valenlysm29/FdD_EQUIPO02/Proyecto/Módulo Mecánico/Certificados/Rosita Espinola/Certificados de Rosita Espinola-1.pdf

ROSITA ABANTO

April 30, 2026

Detailed Drawings

ROSITA ABANTO

Introduction to Sketching

April 30, 2026

ROSITA ABANTO

Introduction to Part Studios

April 30, 2026

ROSITA ABANTO

April 30, 2026

Introduction to Onshape Assemblies

Onshape Fundamentals

April 30, 2026

ROSITA ABANTO

ROSITA ABANTO

CAD Basics

April 30, 2026
