valenlysm29/FdD_EQUIPO02/Proyecto/Módulo Mecánico/Certificados/Ayme Canchari/Certificados de Ayme Canchari-1.pdf

Onshape Fundamentals

April 30, 2026

Ayme Canchari

Ayme Canchari

Advanced Onshape Assemblies

May 21, 2026

Ayme Canchari

April 30, 2026

Introduction to Drawings

Ayme Canchari

April 30, 2026

Detailed Drawings

Ayme Canchari

Introduction to Sketching

April 30, 2026

Ayme Canchari

April 30, 2026

Introduction to Onshape Assemblies
