valenlysm29/FdD_EQUIPO02/FundDiseño/Talleres/Taller 7/Taller 7_certificados/Perez Salvatierra, Maria Fernanda/Maria Fernanda Perez Salvatierra (1).pdf

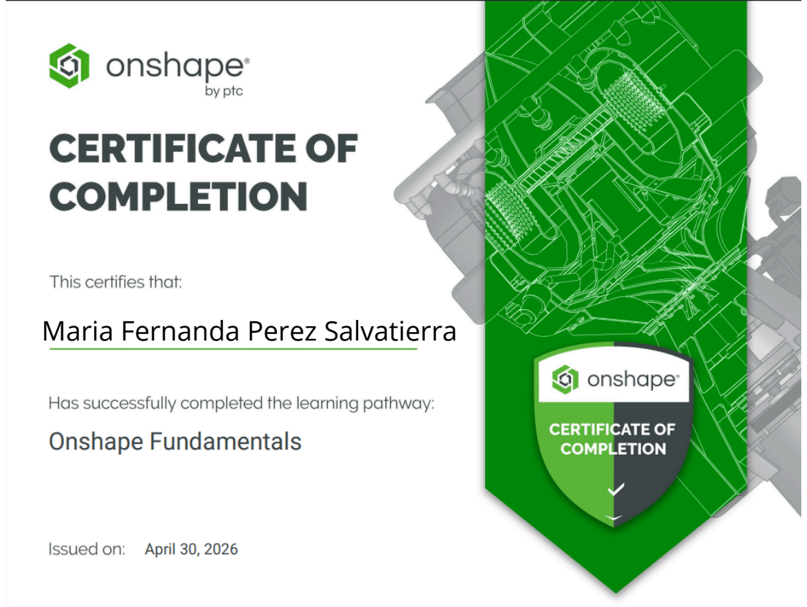
[picture p95: page 1]

Maria Fernanda Perez Salvatierra
