valenlysm29/FdD_EQUIPO02/Recursos/Imágenes/Patentes/Atrapanieblas Multifuncional para Riego.pdf

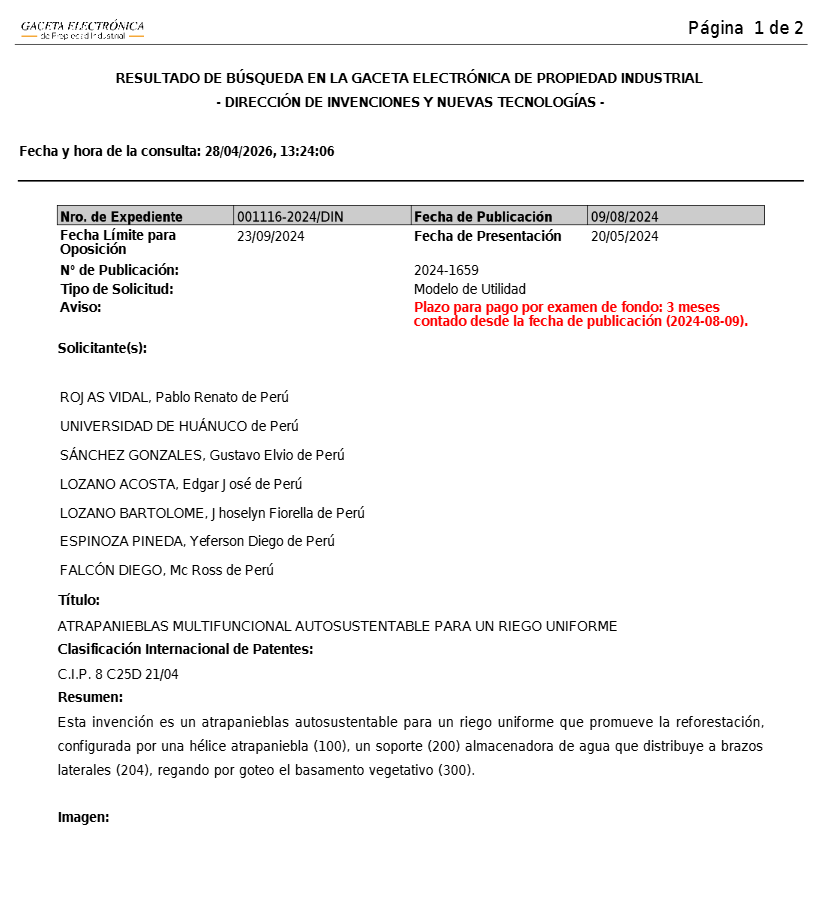
[picture p96: page 1]
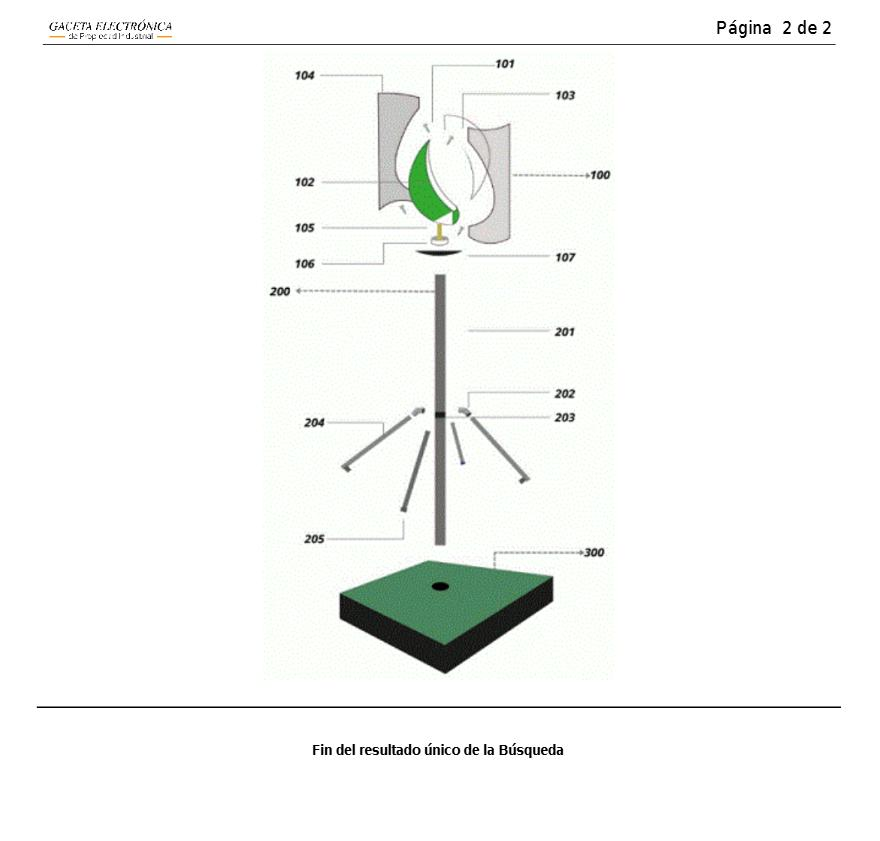
[picture p97: page 2]
