valenlysm29/FdD_EQUIPO02/Proyecto/Módulo Mecánico/version 1.0/Onshape/ENLACE_DE_ONSHAPE CORREGIDO.md

# LINK -Diseños CAD

## CAJA 1
[CAJA 1 en Onshape](https://cad.onshape.com/documents/41e83d5ab6f618795a68725b/w/8556b80361a83598566b62ff/e/50794cb14106d23a55636a70)

## CAJA 2
[CAJA 2 en Onshape](https://cad.onshape.com/documents/738e8bcb6a7b22823f326922/w/f9162c663f5a3e53b6d7ac40/e/0bef76de6ebbbb28ef8982e9)
