valenlysm29/FdD_EQUIPO02/Proyecto/Módulo Mecánico/version 2.0/Boceto/Boceto2.2.jpeg

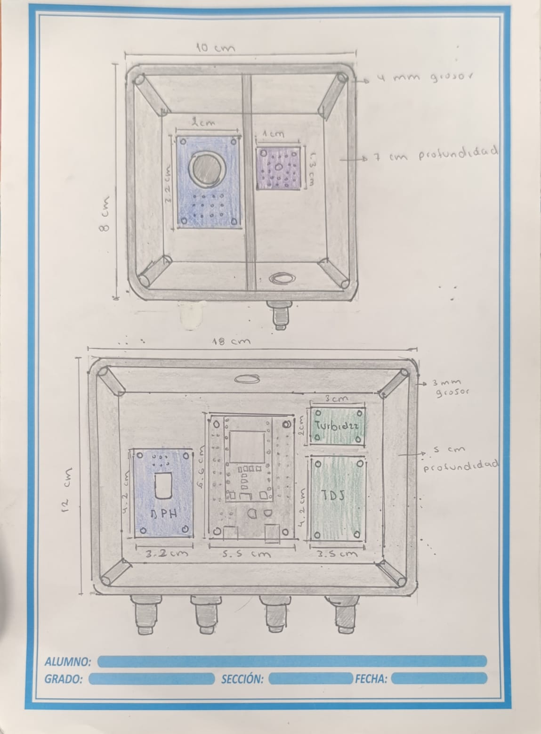
Proyecto/Módulo Mecánico/version 2.0/Boceto/Boceto2.2.jpeg
