valenlysm29/FdD_EQUIPO02/Proyecto/Módulo Mecánico/VFINAL/Boceto/Boceto interno.jpeg

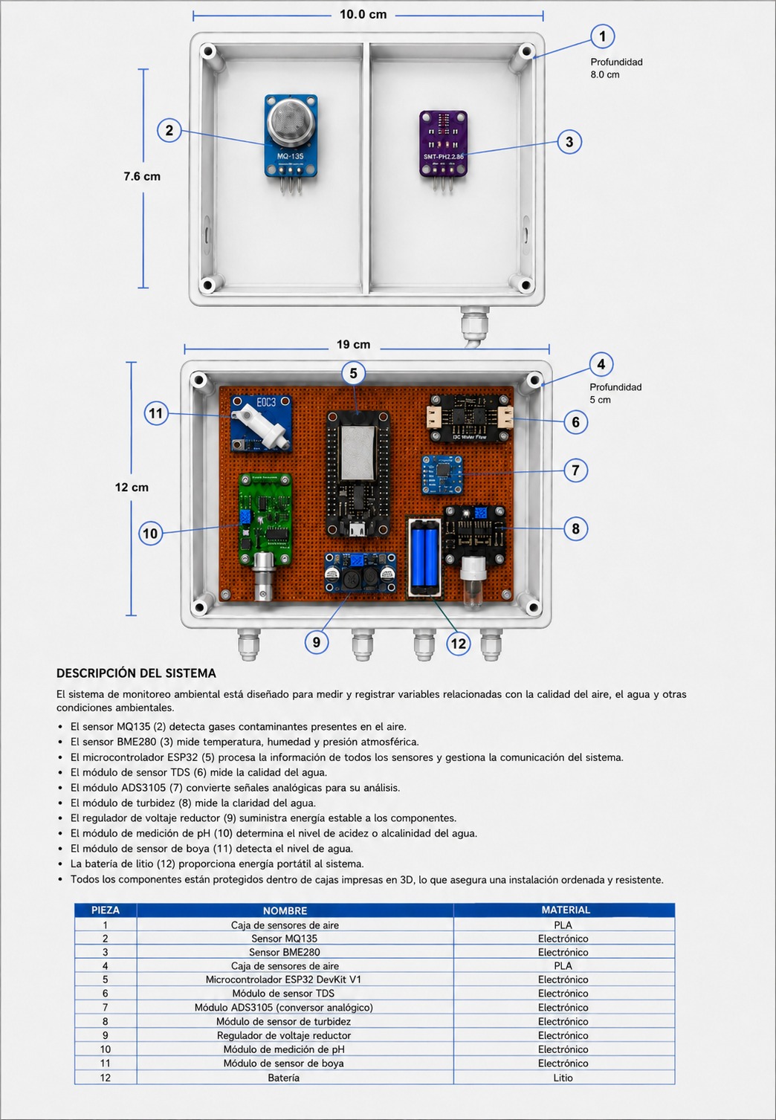
Proyecto/Módulo Mecánico/VFINAL/Boceto/Boceto interno.jpeg
