valenlysm29/FdD_EQUIPO02/Proyecto/Módulo Mecánico/VFINAL/Boceto/sistema atrapanieblas con monitoreo.jpeg

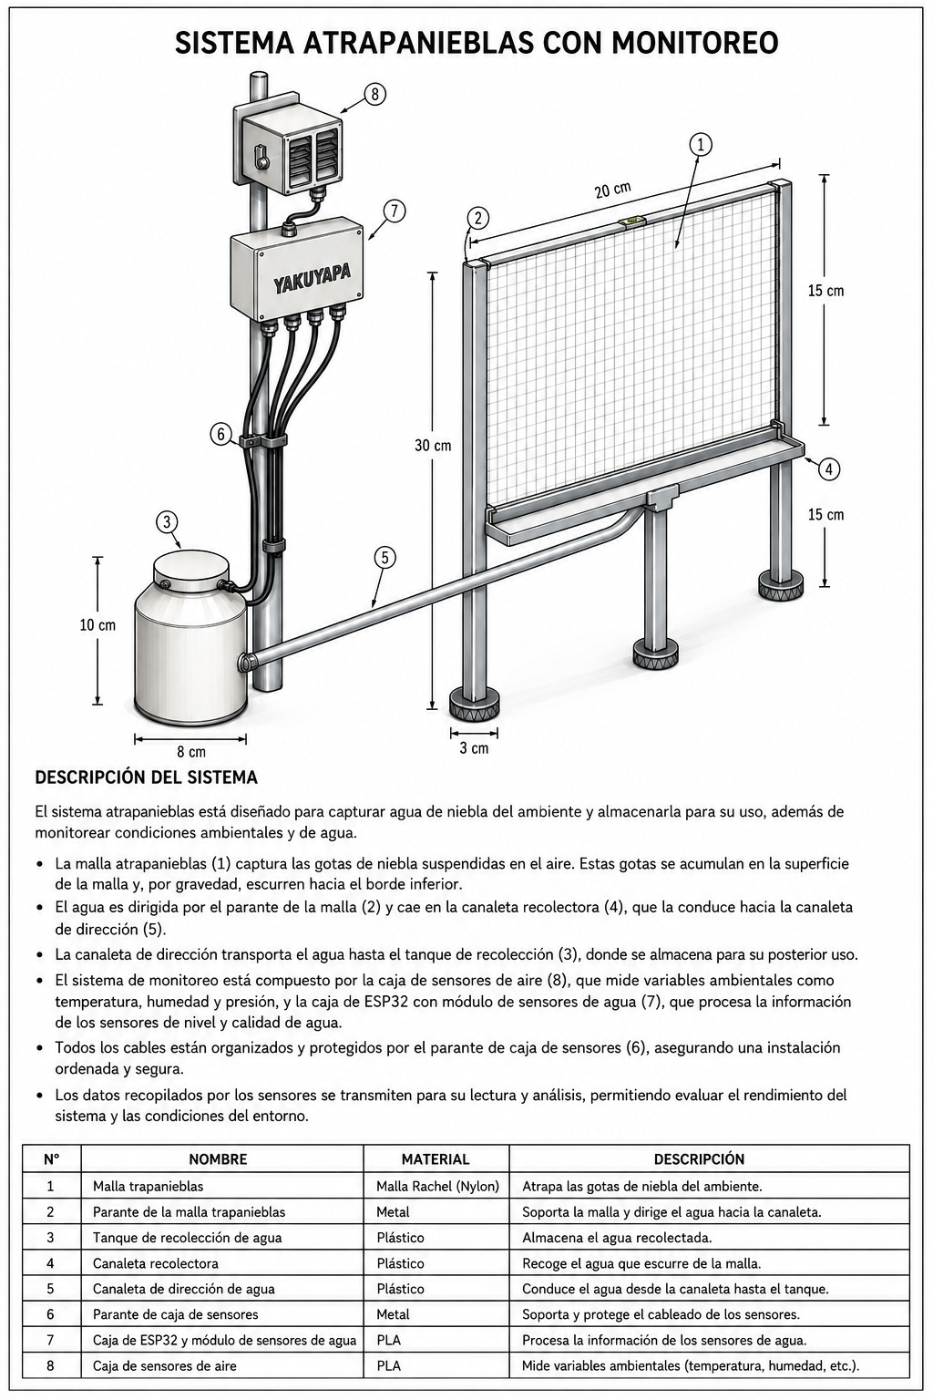
Proyecto/Módulo Mecánico/VFINAL/Boceto/sistema atrapanieblas con monitoreo.jpeg
