valenlysm29/FdD_EQUIPO02/Proyecto/Módulo Mecánico/VFINAL/Boceto/Sistema Atrapanieblas.jpeg

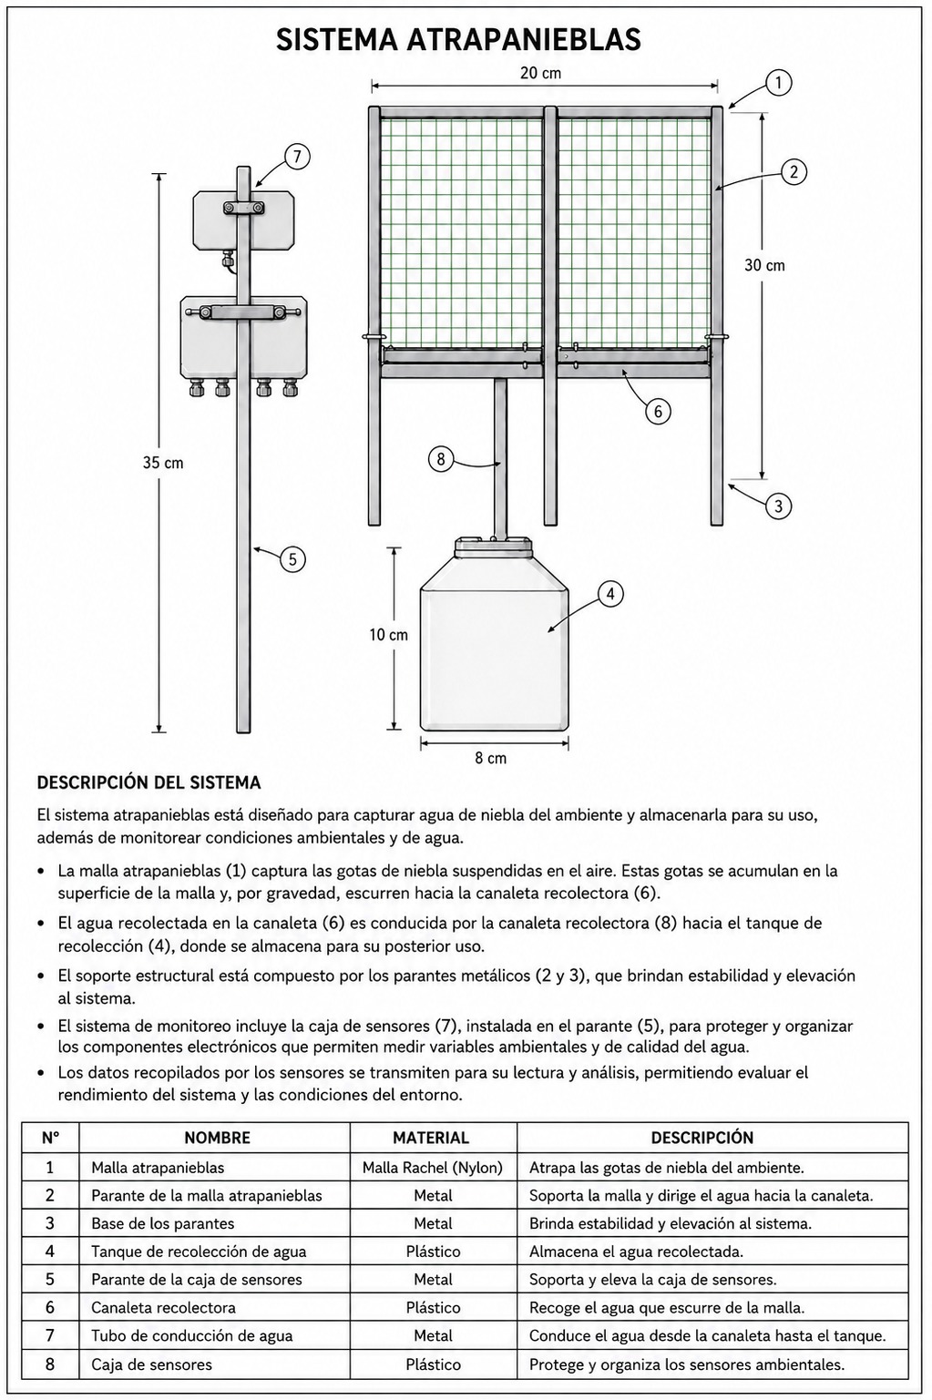
Proyecto/Módulo Mecánico/VFINAL/Boceto/Sistema Atrapanieblas.jpeg
