valenlysm29/FdD_EQUIPO02/Proyecto/Módulo Mecánico/VFINAL/Boceto/Vista por fuera de las cajas.jpeg

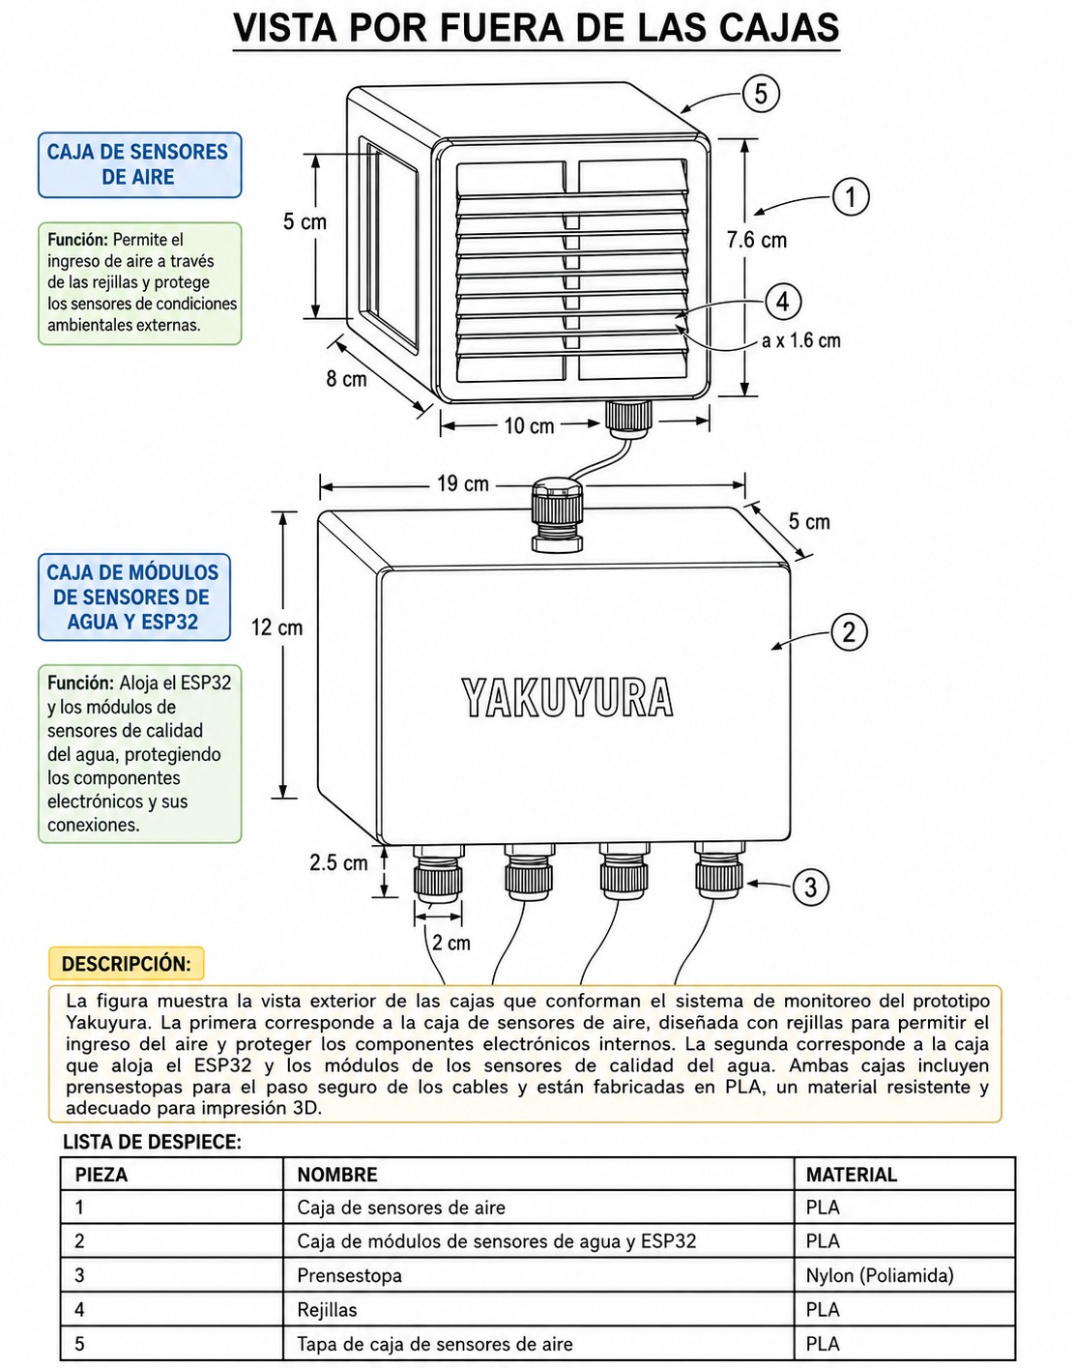
Proyecto/Módulo Mecánico/VFINAL/Boceto/Vista por fuera de las cajas.jpeg
