valenlysm29/FdD_EQUIPO02/Recursos/Imágenes/Imágenes/Fotos_Adicionales/PATENTE_04_A.png

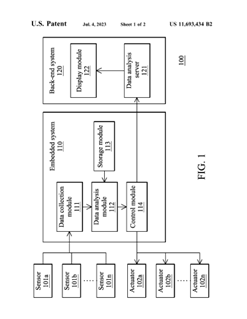
Recursos/Imágenes/Imágenes/Fotos_Adicionales/PATENTE_04_A.png
