valenlysm29/FdD_EQUIPO02/Recursos/Imágenes/Imágenes/Fotos_Adicionales/PATENTE_05.png

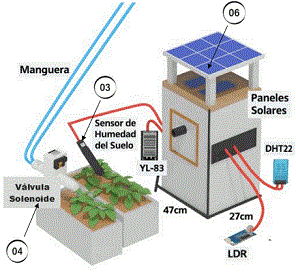
Recursos/Imágenes/Imágenes/Fotos_Adicionales/PATENTE_05.png
