valenlysm29/FdD_EQUIPO02/Proyecto/Módulo Mecánico/version 2.0/Onshape/Partes/Caja Grande/Parte 3 Caja Agua.stl

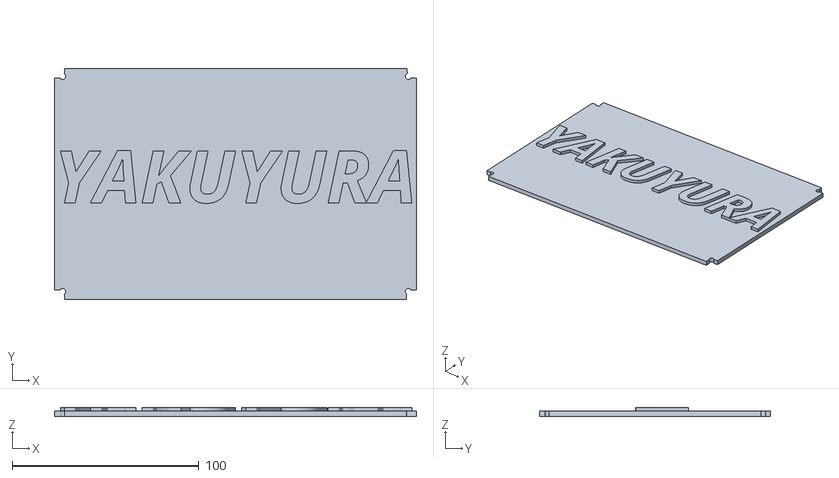
[picture p126: CAD file, 2026-05-28]
Proyecto/Módulo Mecánico/version 2.0/Onshape/Partes/Caja Grande/Parte 3 Caja Agua.stl
194.0 x 124.0 x 5.00
