valenlysm29/FdD_EQUIPO02/Proyecto/Módulo Electrónico/version 2.0/ESQUEMATICO V2.0.pdf

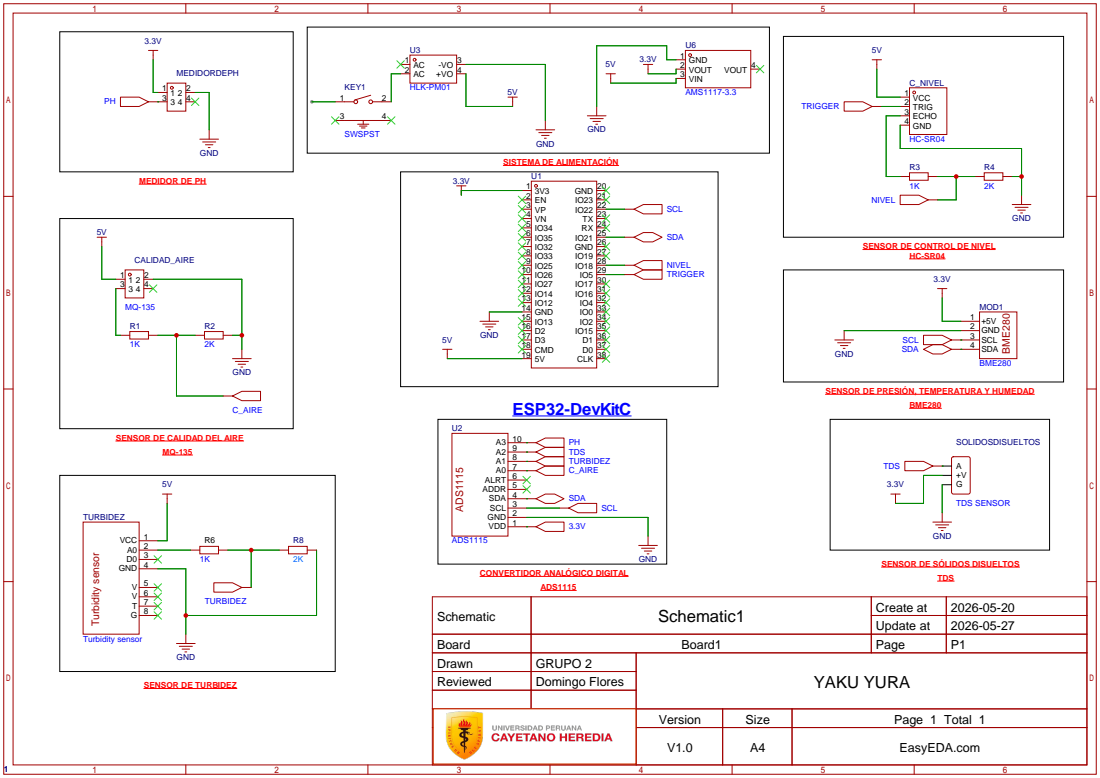
[picture p127: page 1]

SENSOR DE CONTROL DE NIVEL

SENSOR DE PRESIÓN, TEMPERATURA Y HUMEDAD

SENSOR DE CALIDAD DEL AIRE

SENSOR DE SÓLIDOS DISUELTOS

Schematic | Schematic1 | Create at | 2026-05-20

Update at | 2026-05-27

Board | Board1 | Page | P1
Drawn | GRUPO 2 | YAKU YURA
Reviewed | Domingo Flores

Version | Size | Page 1 Total 1
V1.0 | A4 | EasyEDA.com
