valenlysm29/FdD_EQUIPO02/Proyecto/Módulo Mecánico/Certificados/Maria Fernanda/certificados de maria fernadnda perez-1.pdf

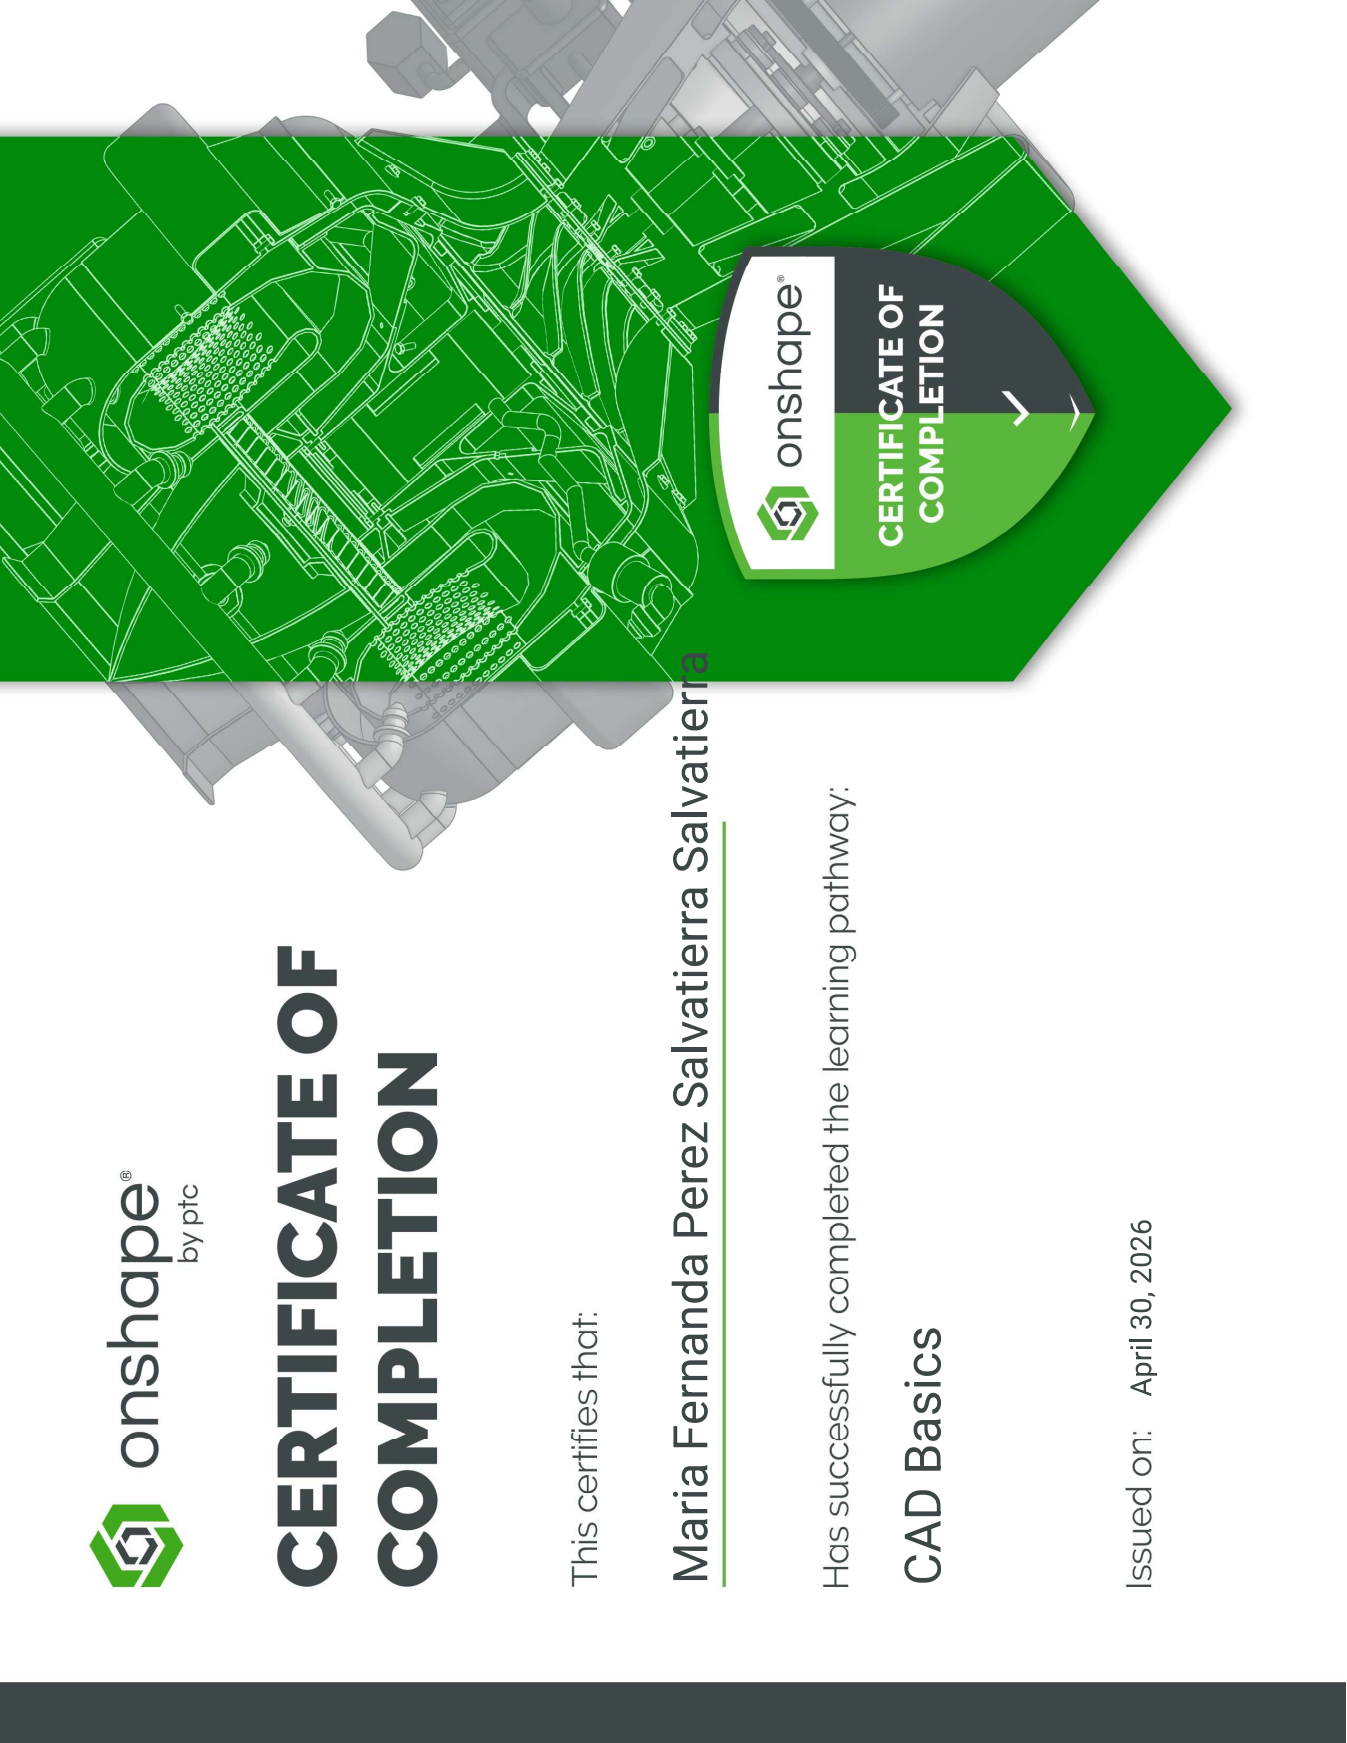
[picture p141: page 1]

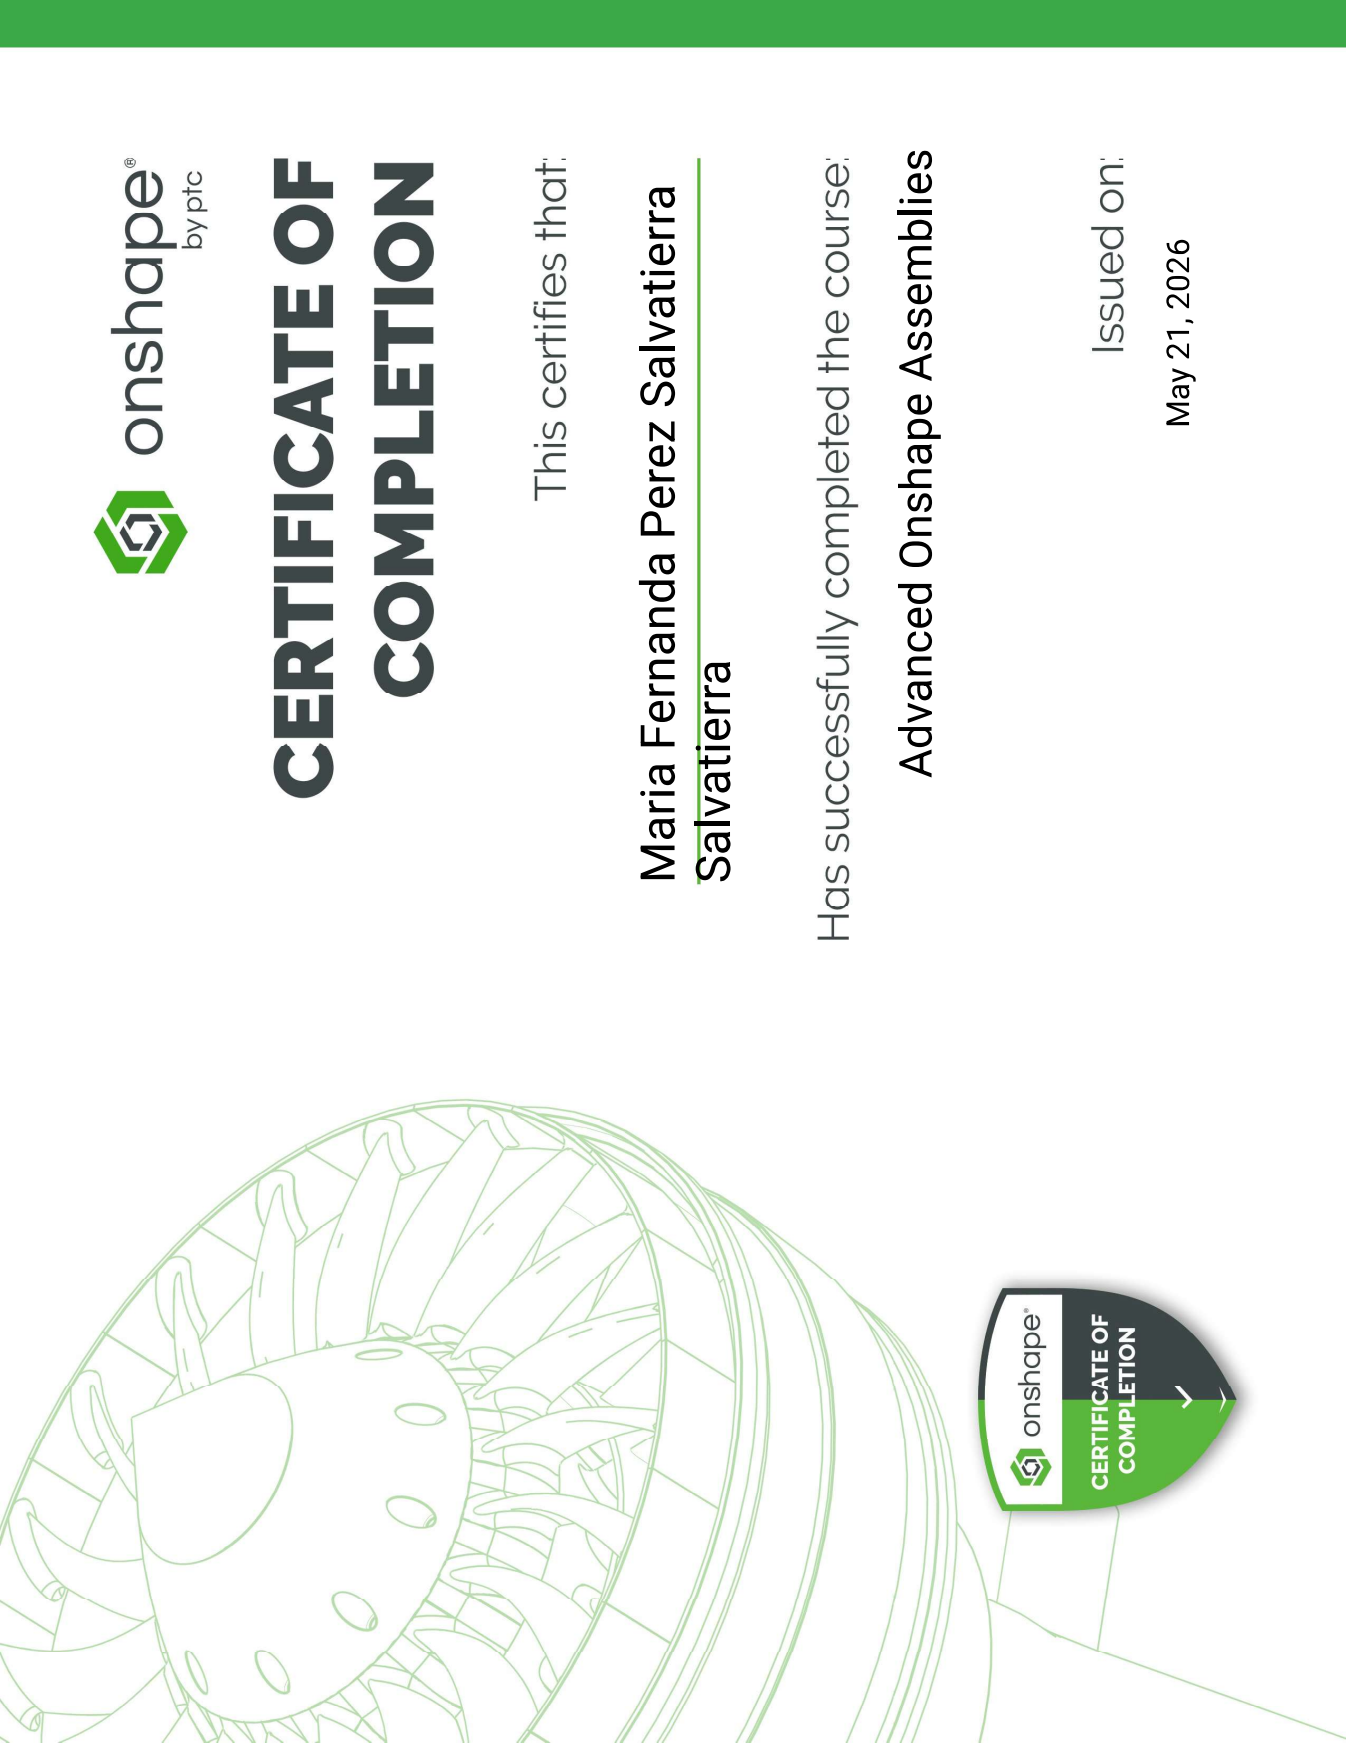
[picture p142: page 2]

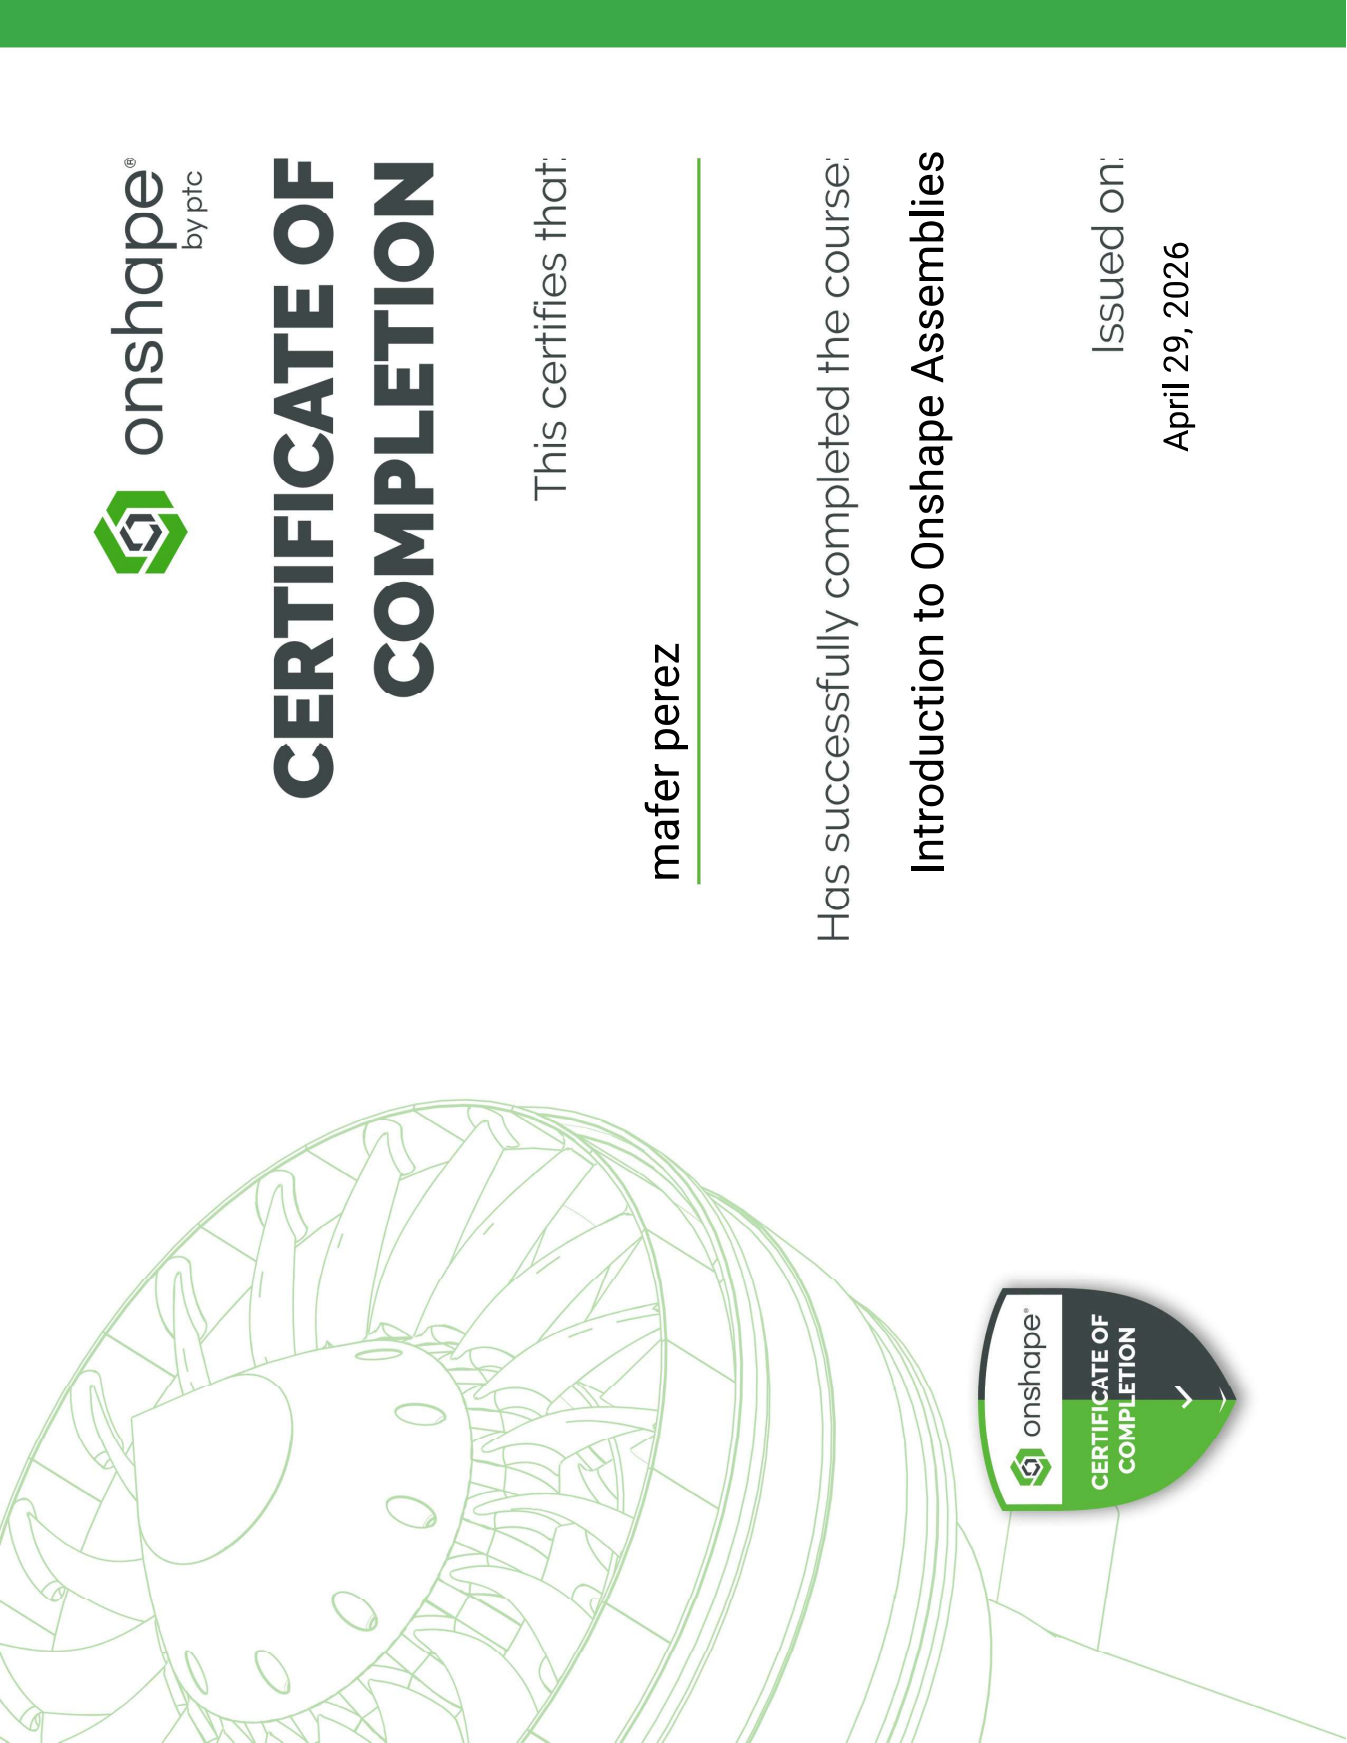
[picture p143: page 3]

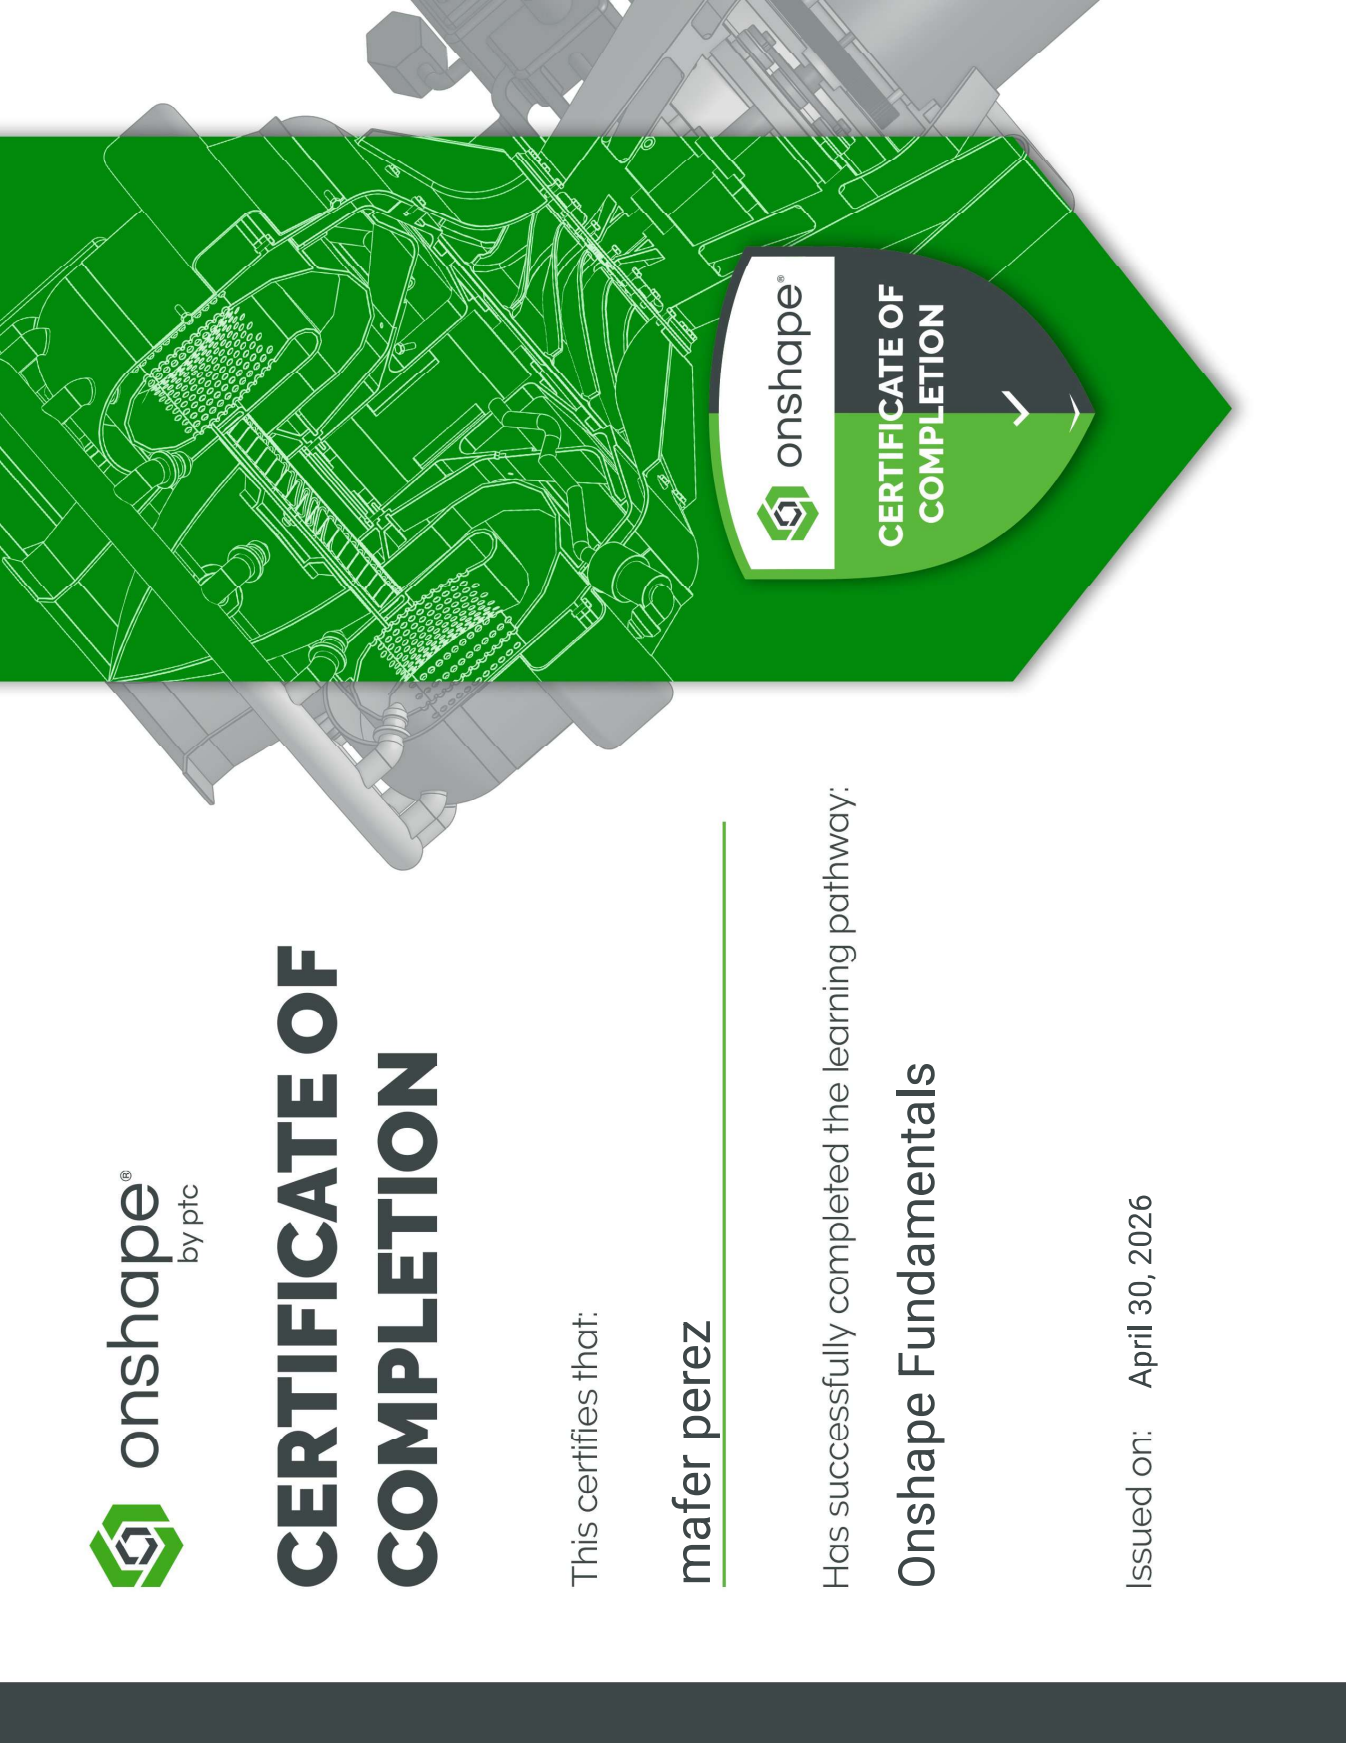
[picture p144: page 4]

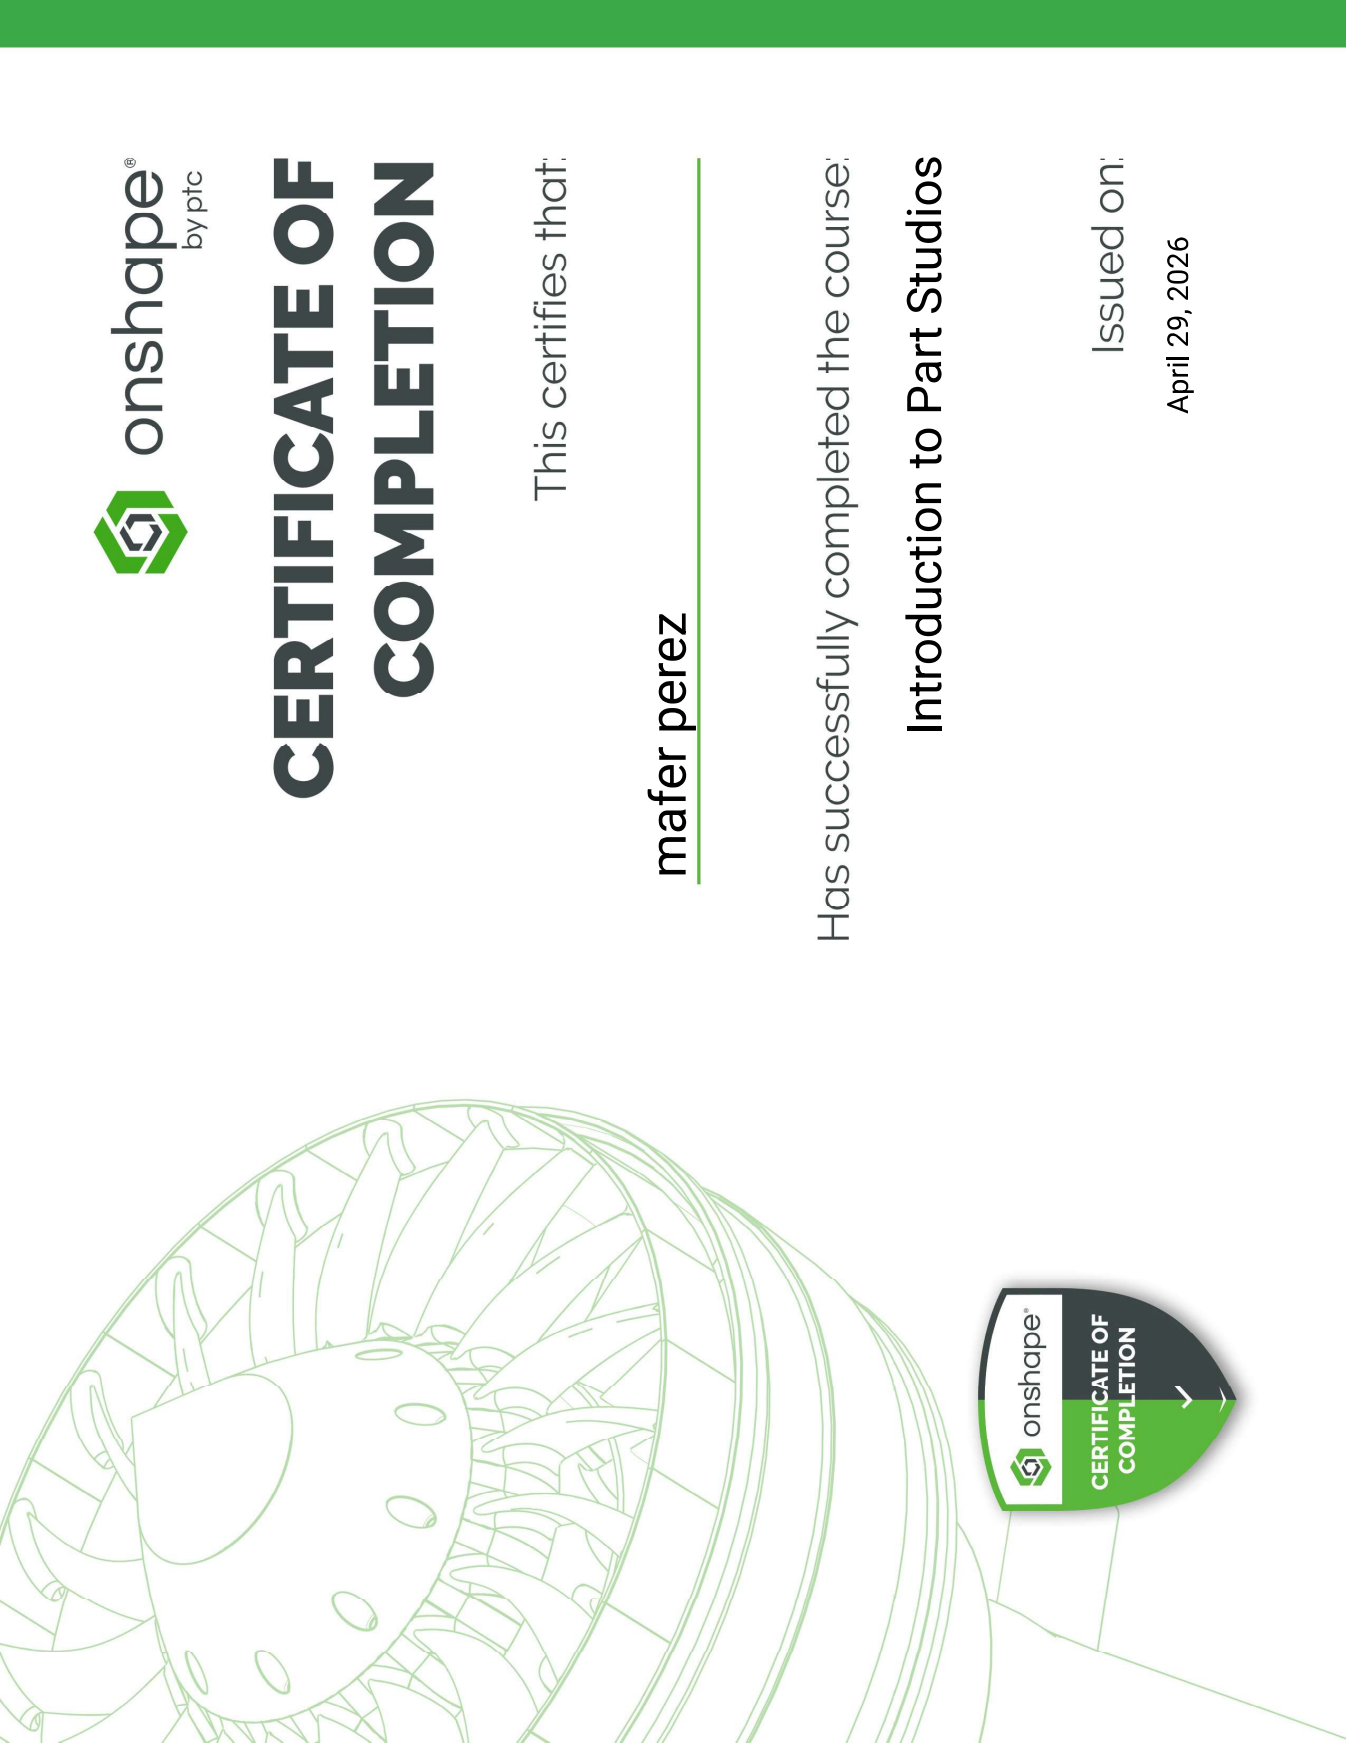
[picture p145: page 5]
