valenlysm29/FdD_EQUIPO02/Proyecto/Módulo Mecánico/VFINAL/ONSHAPE/PLANOS/Plano tapa caja grande VFINAL.pdf

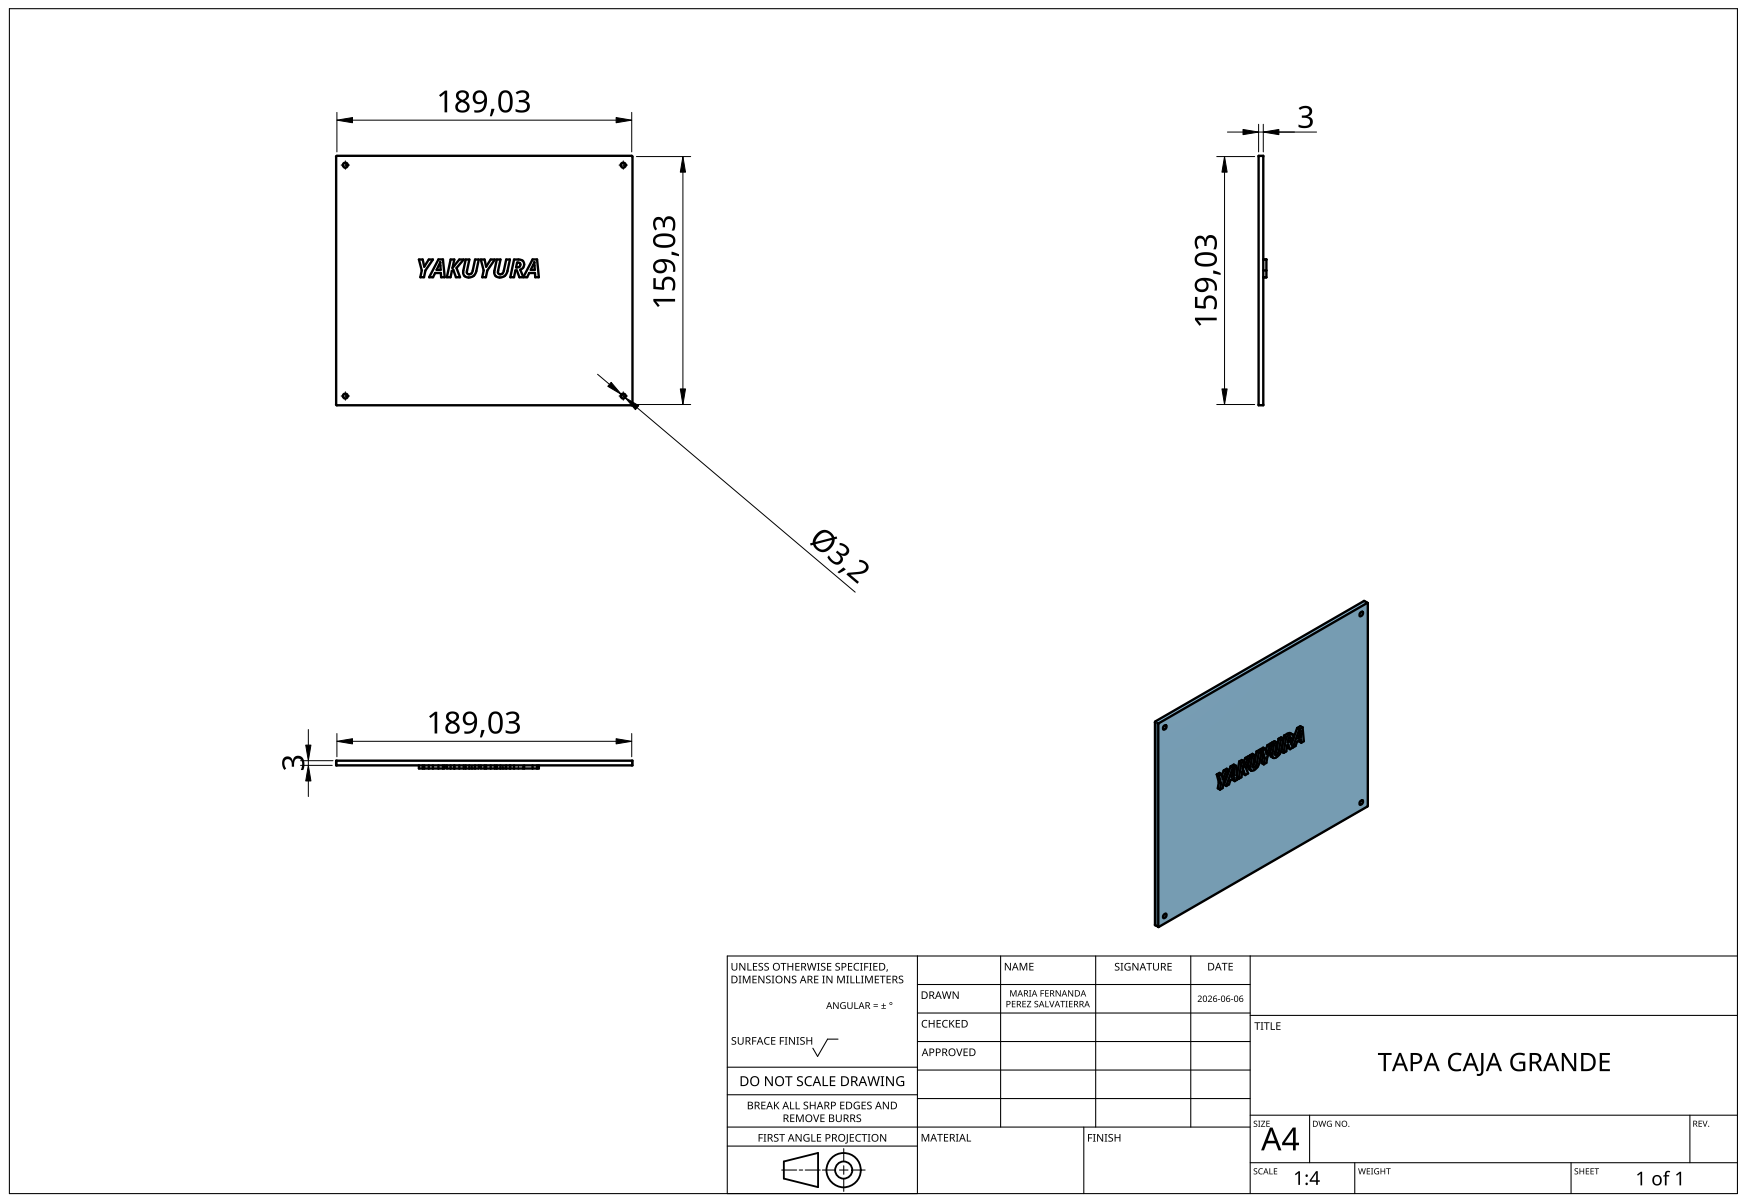
[picture p146: page 1]
