valenlysm29/FdD_EQUIPO02/Proyecto/Módulo Mecánico/VFINAL/ONSHAPE/PLANOS/Plano tapa caja chica VFINAL.pdf

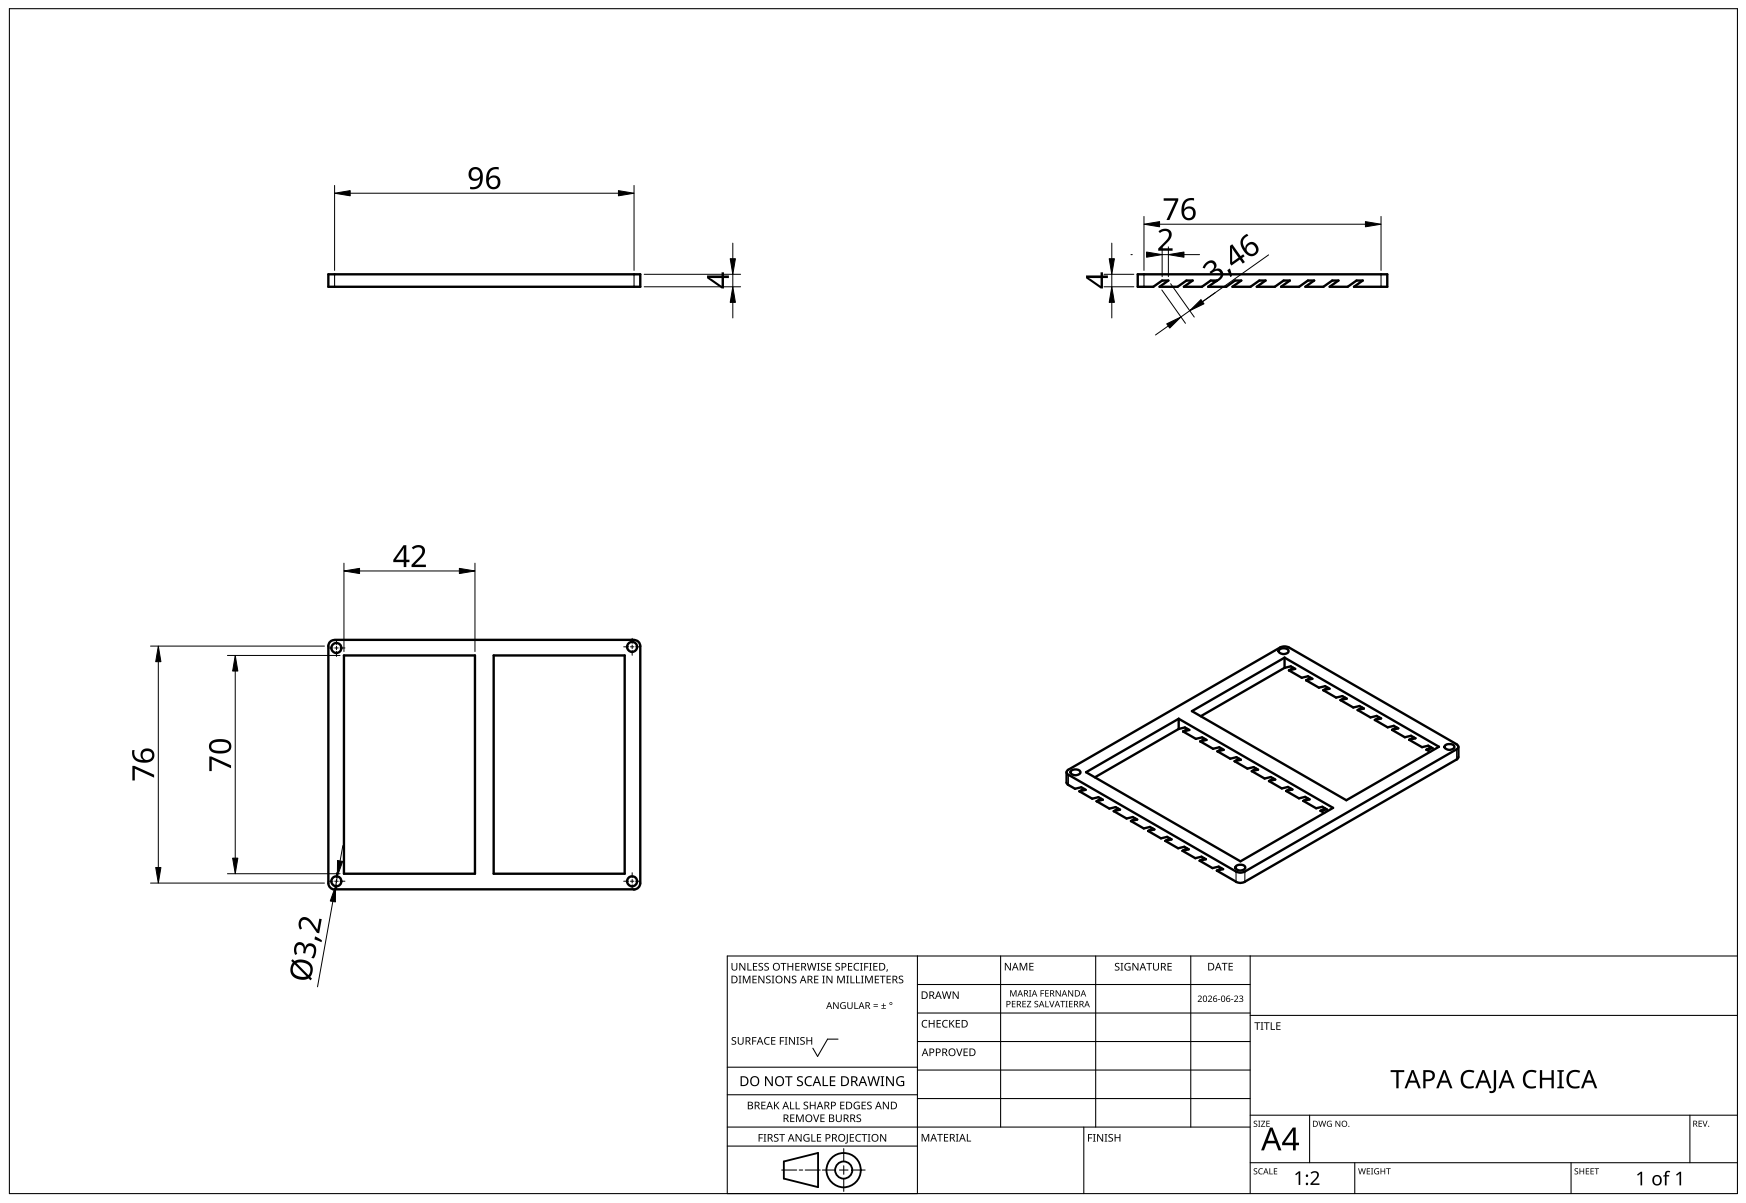
[picture p147: page 1]
