valenlysm29/FdD_EQUIPO02/Proyecto/Módulo Mecánico/VFINAL/ONSHAPE/PLANOS/Plano reja caja chica VFINAL.pdf

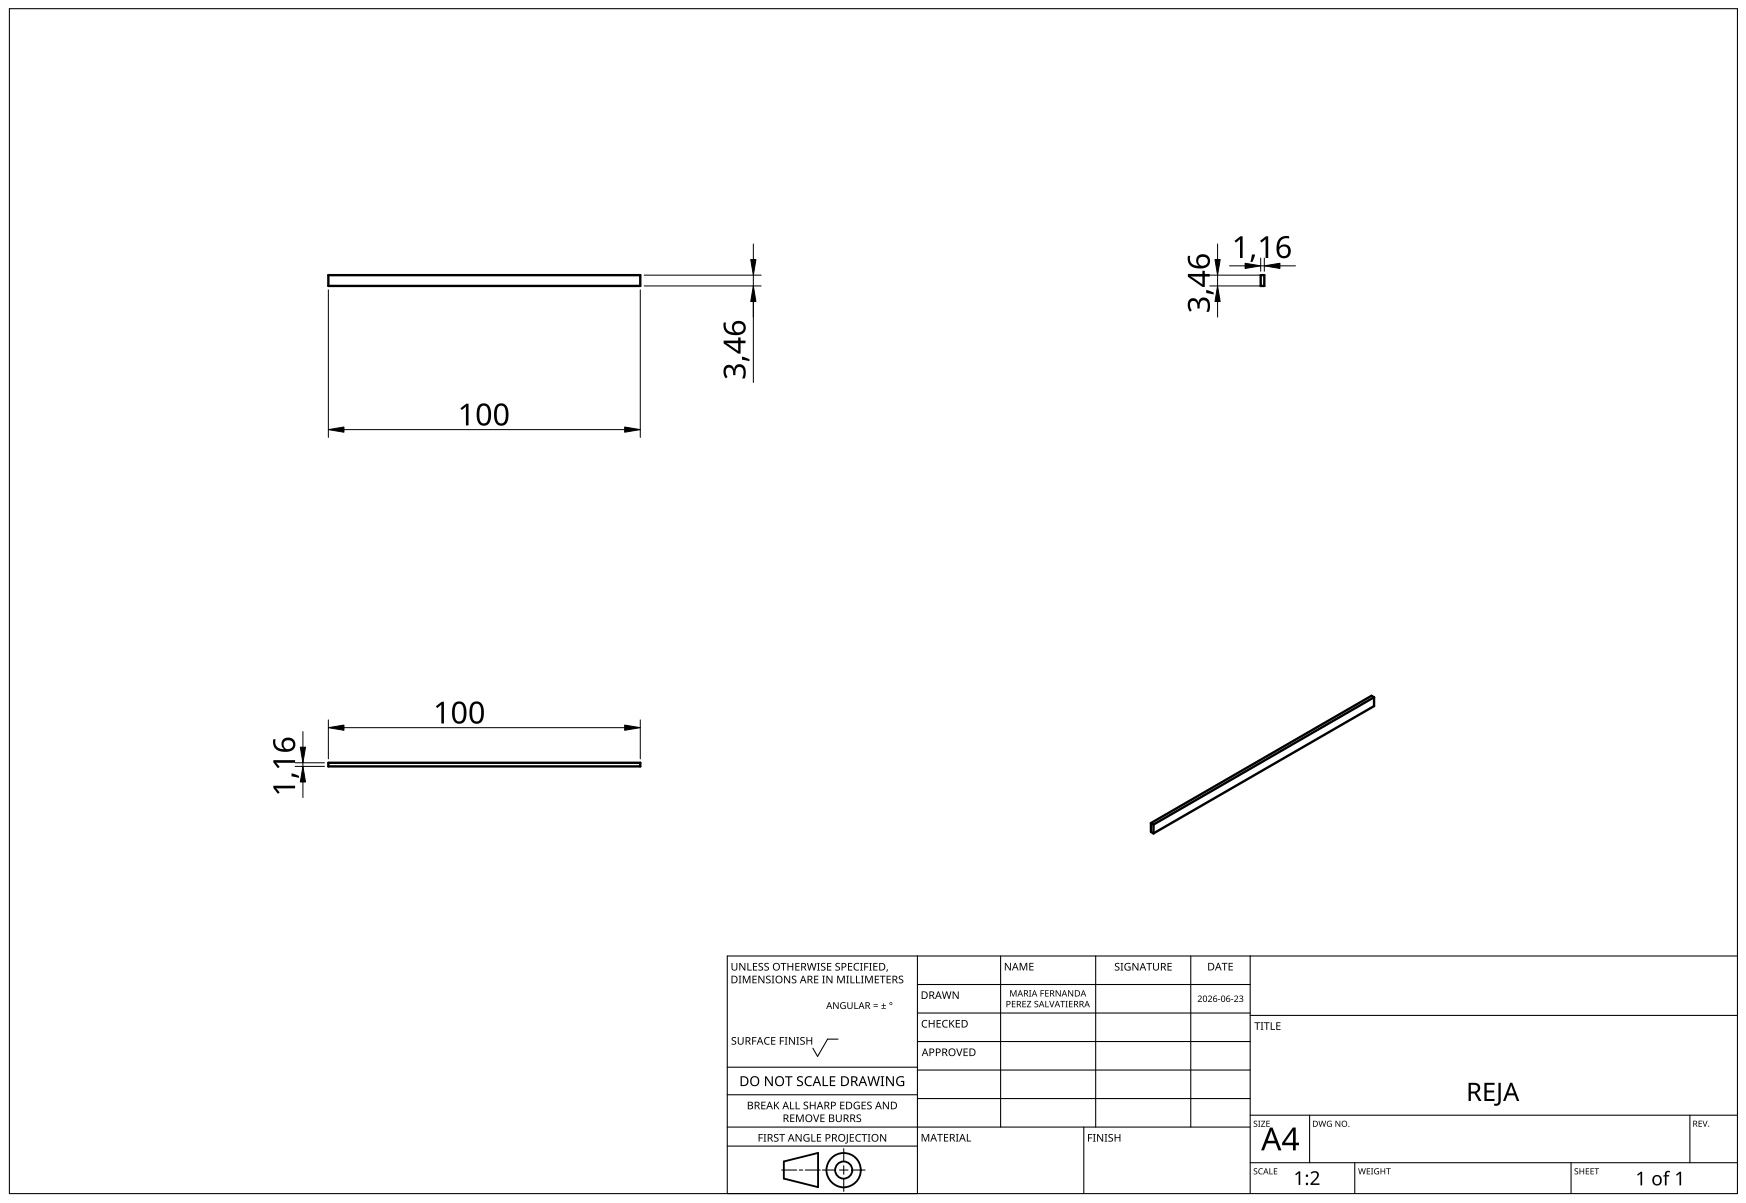
[picture p148: page 1]
