valenlysm29/FdD_EQUIPO02/Proyecto/Módulo Mecánico/VFINAL/ONSHAPE/PLANOS/Plano caja sensor de aire VFINAL.pdf

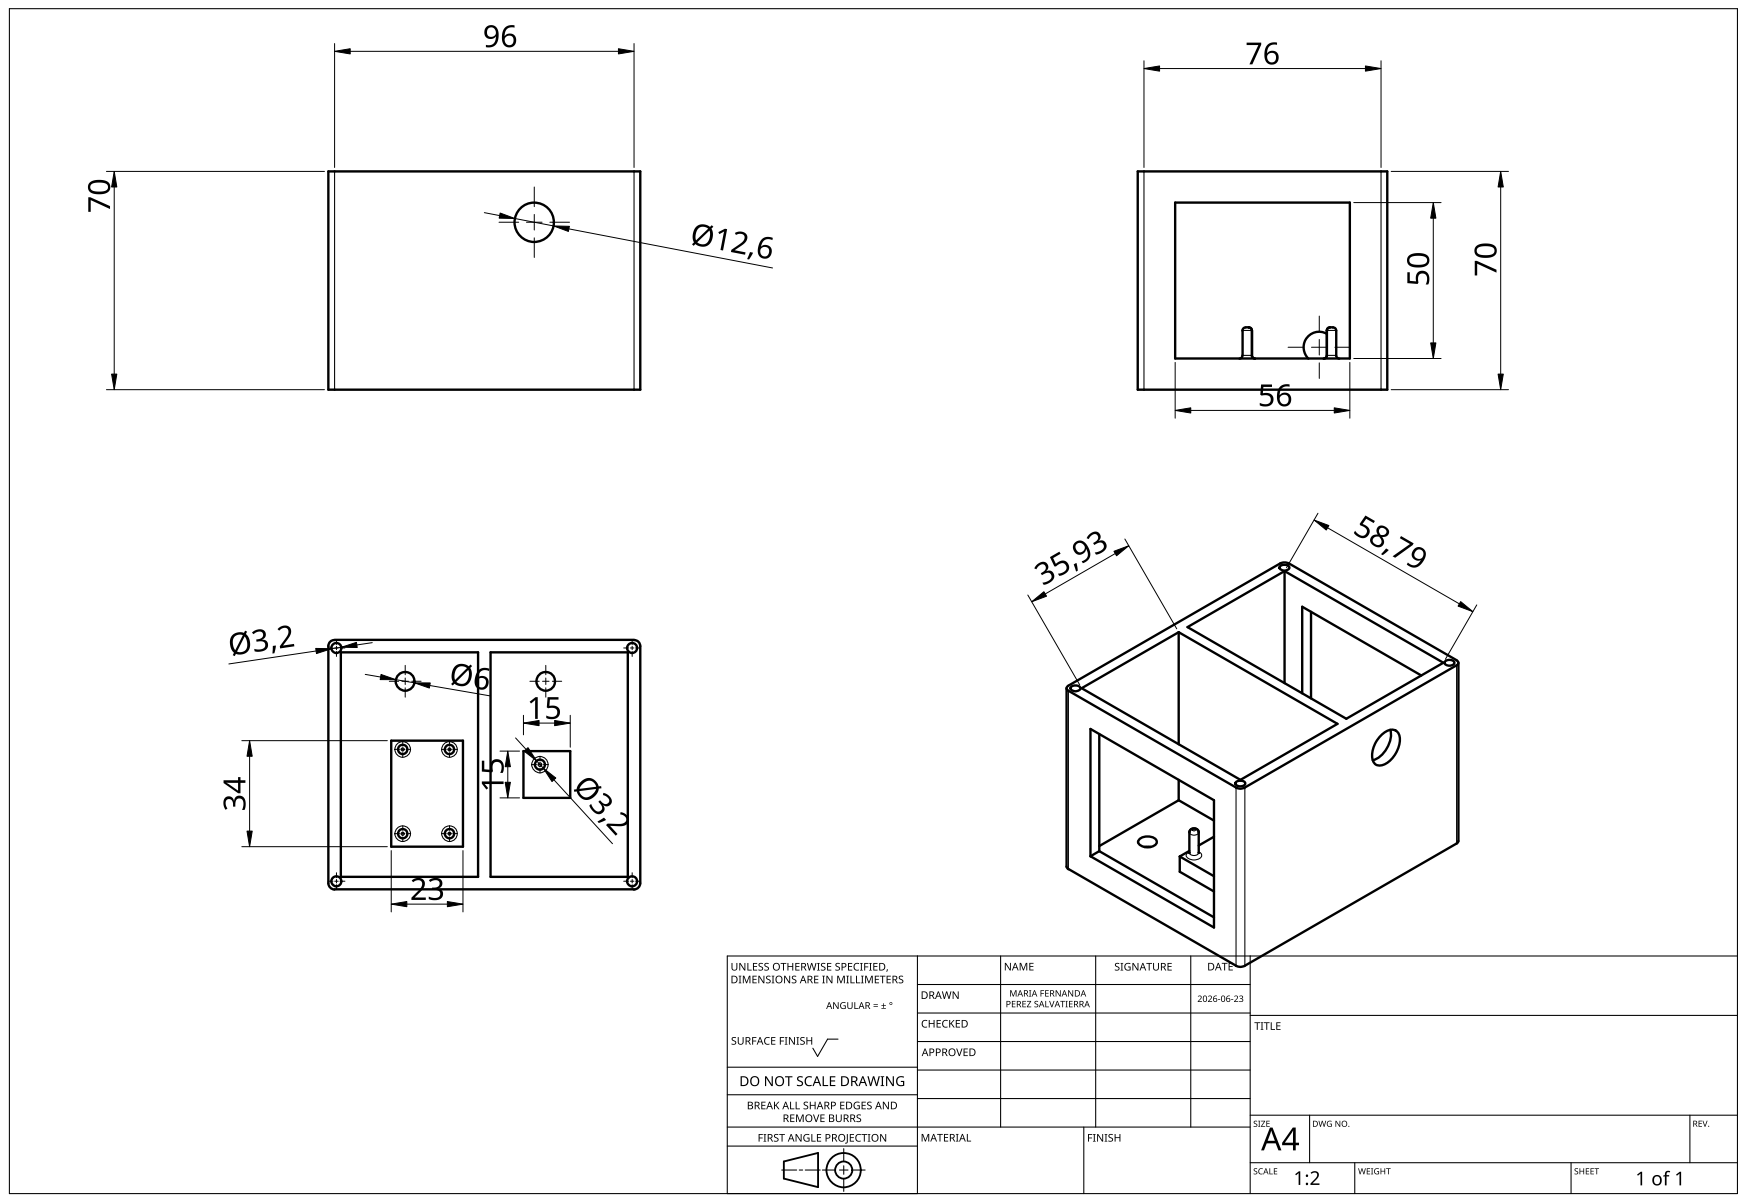
[picture p149: page 1]
