valenlysm29/FdD_EQUIPO02/Proyecto/Módulo Mecánico/VFINAL/ONSHAPE/PLANOS/Plano caja grande VFINAL.pdf

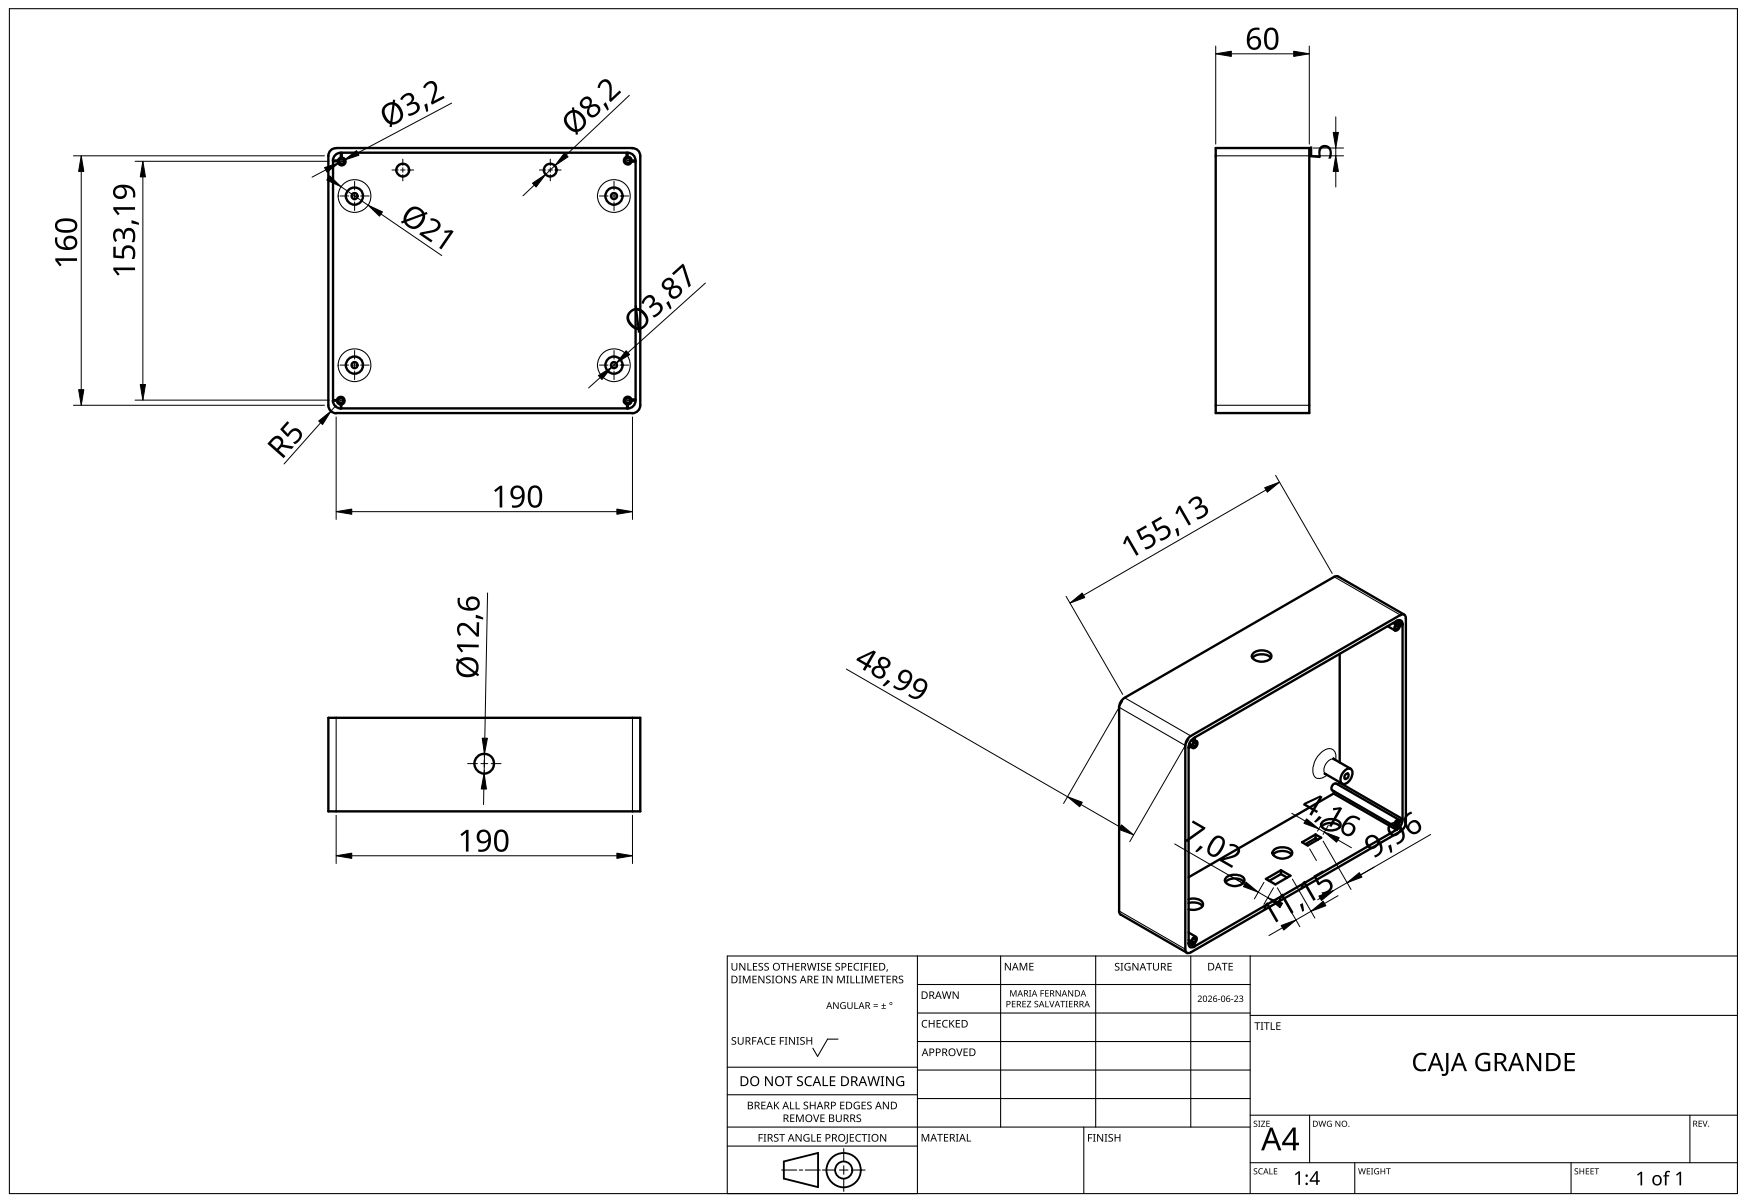
[picture p150: page 1]
