valenlysm29/FdD_EQUIPO02/Proyecto/Módulo Mecánico/version 2.0/Onshape/Planos/Caja Grande/Part 1 Caja Agua Drawing 4.pdf

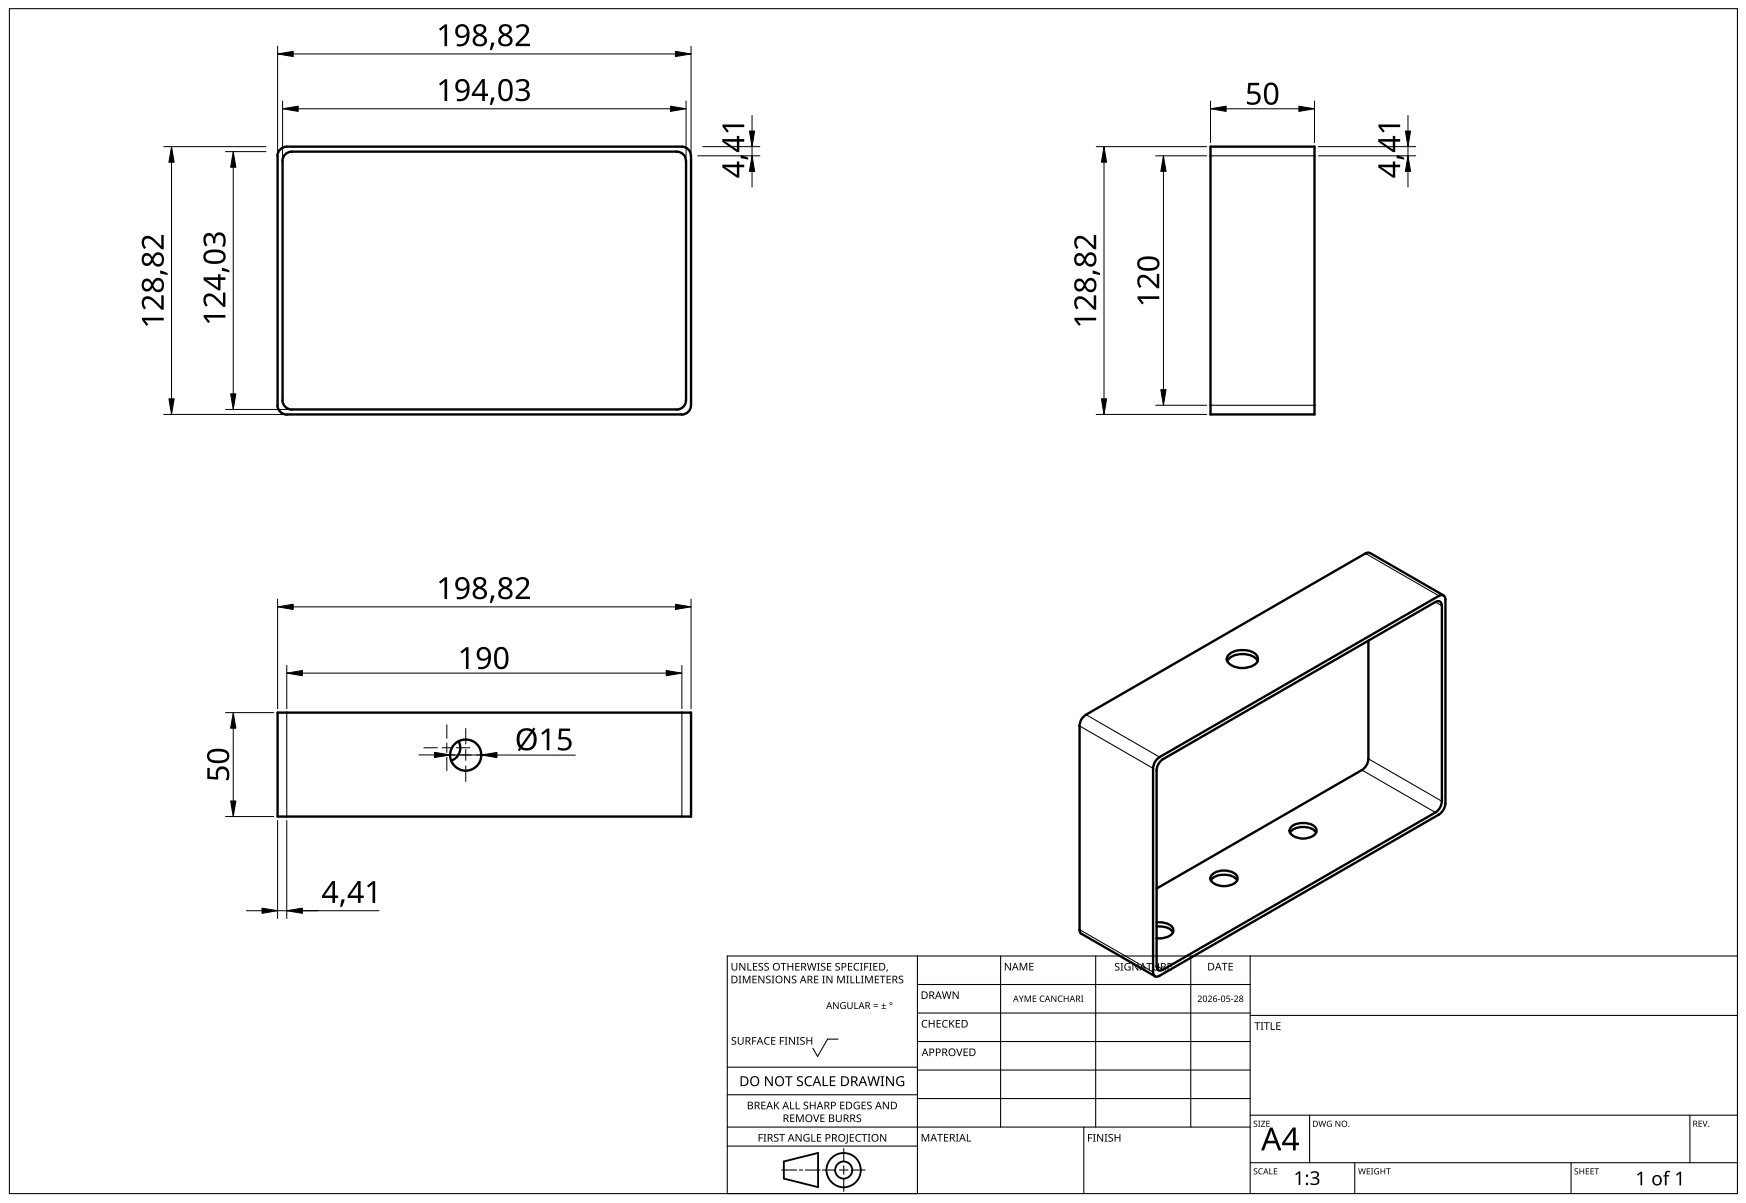
[picture p151: page 1]
