valenlysm29/FdD_EQUIPO02/Proyecto/Módulo Mecánico/version 2.0/Onshape/Planos/Caja Grande/Part 2 Caja Agua Drawing 2.pdf

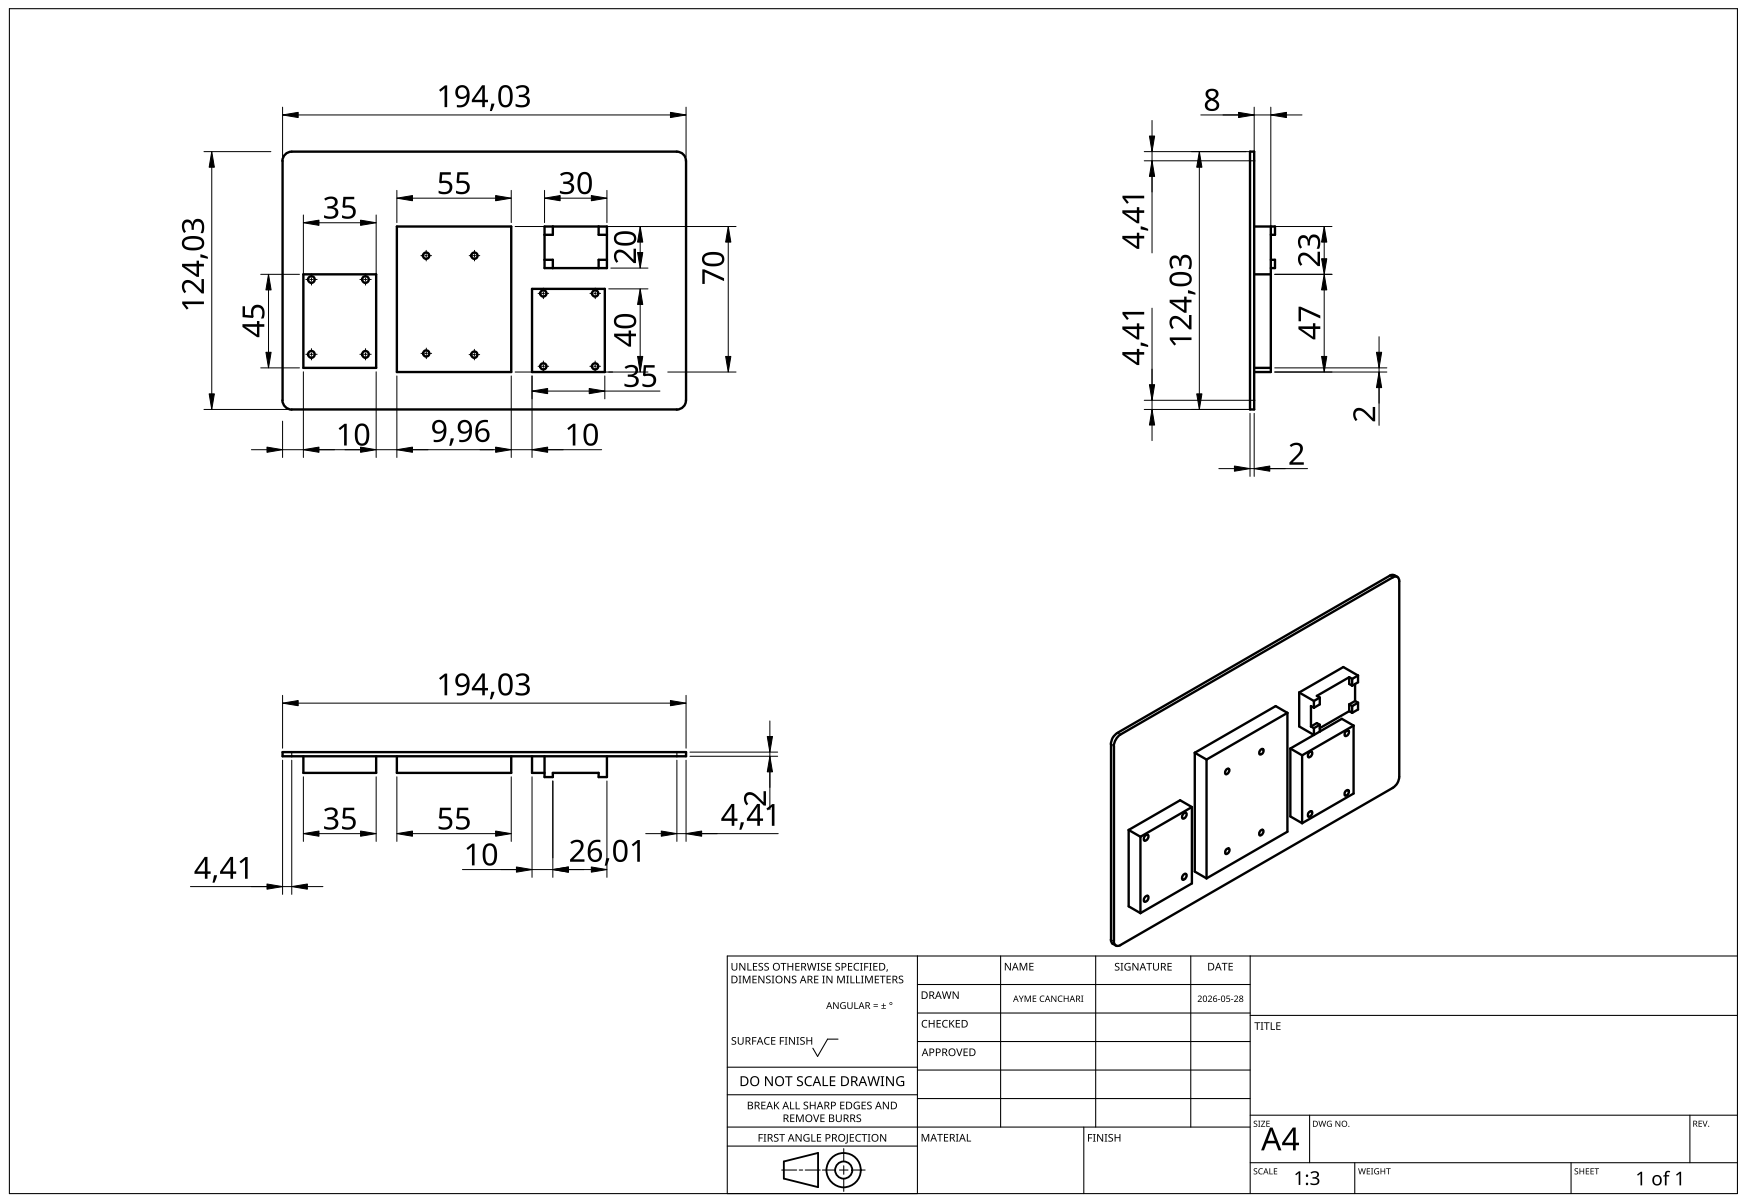
[picture p152: page 1]
