valenlysm29/FdD_EQUIPO02/Proyecto/Módulo Mecánico/version 2.0/Onshape/Planos/Caja Grande/Part 3  Caja Agua Drawing 2.pdf

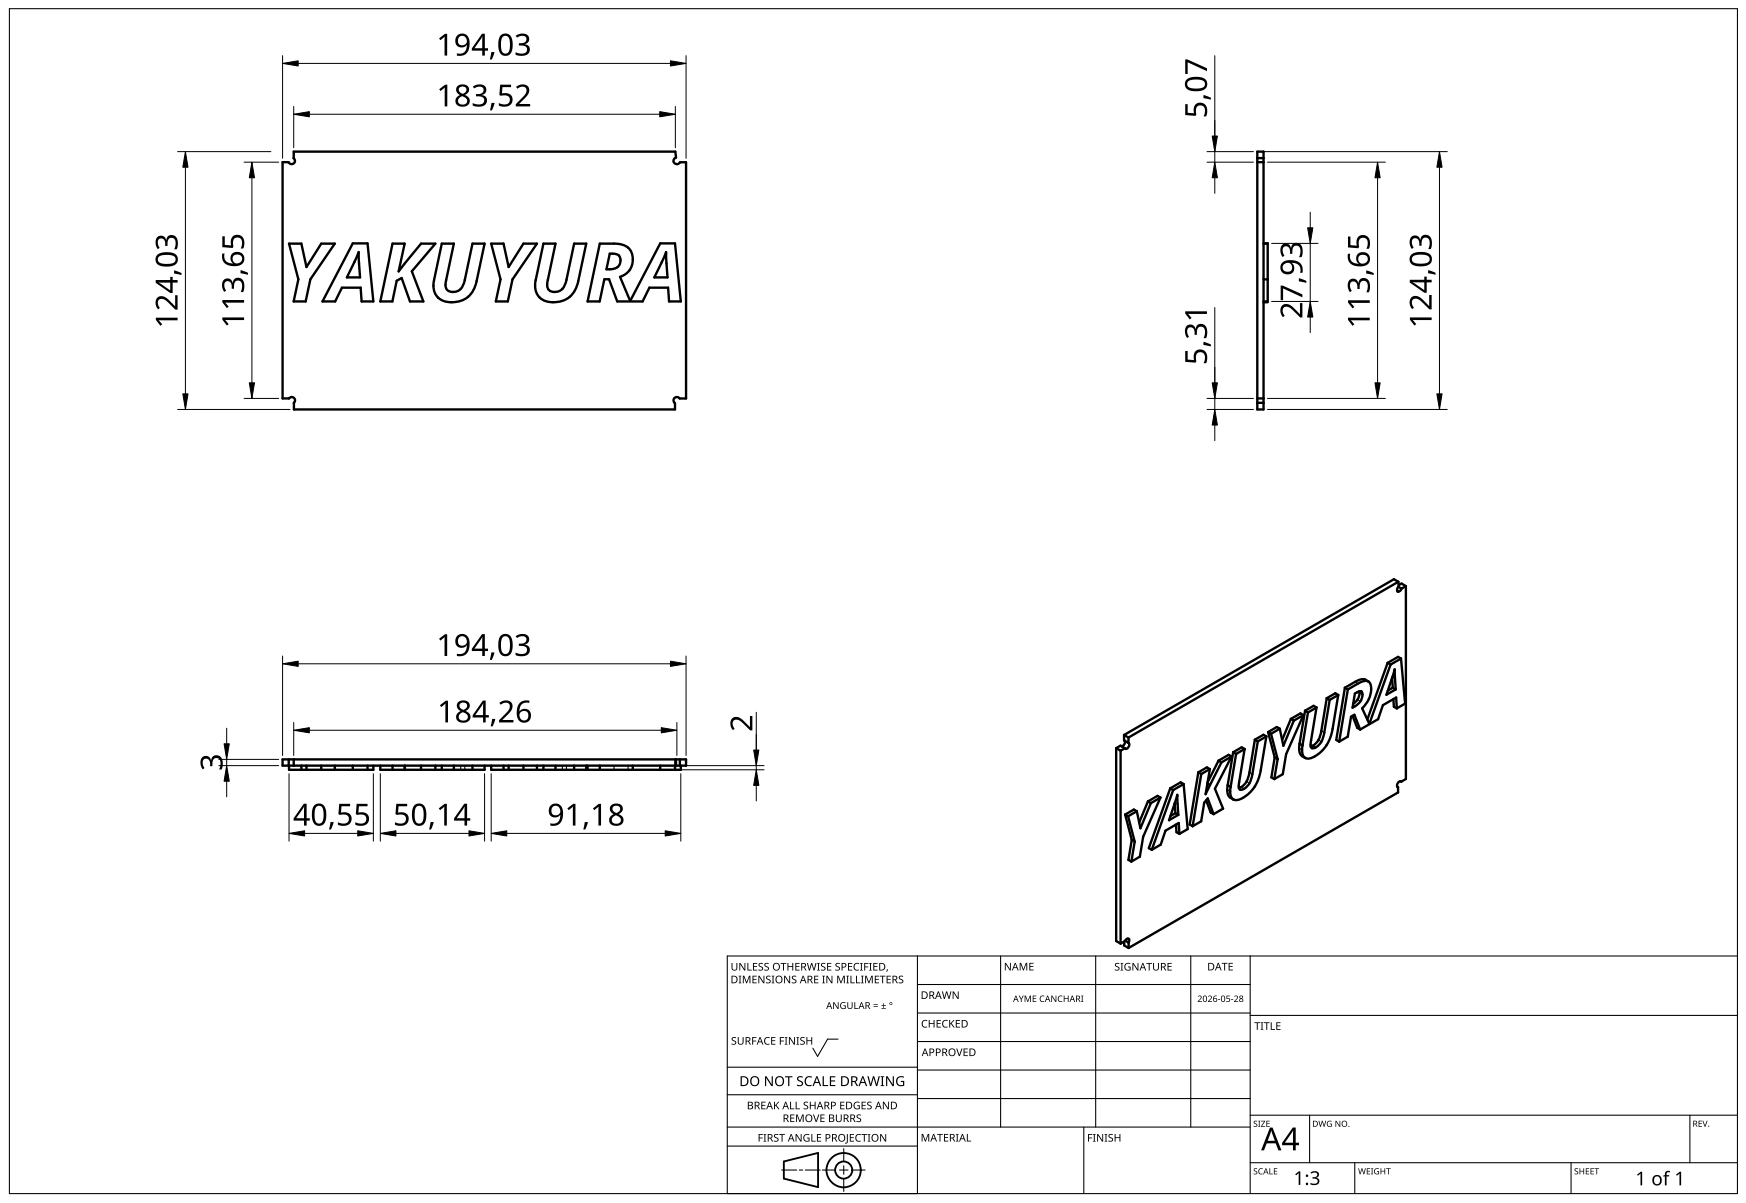
[picture p153: page 1]
