valenlysm29/FdD_EQUIPO02/Proyecto/Módulo Mecánico/version 2.0/Onshape/Planos/Caja Grande/Part 5 Caja Agua Drawing 1.pdf

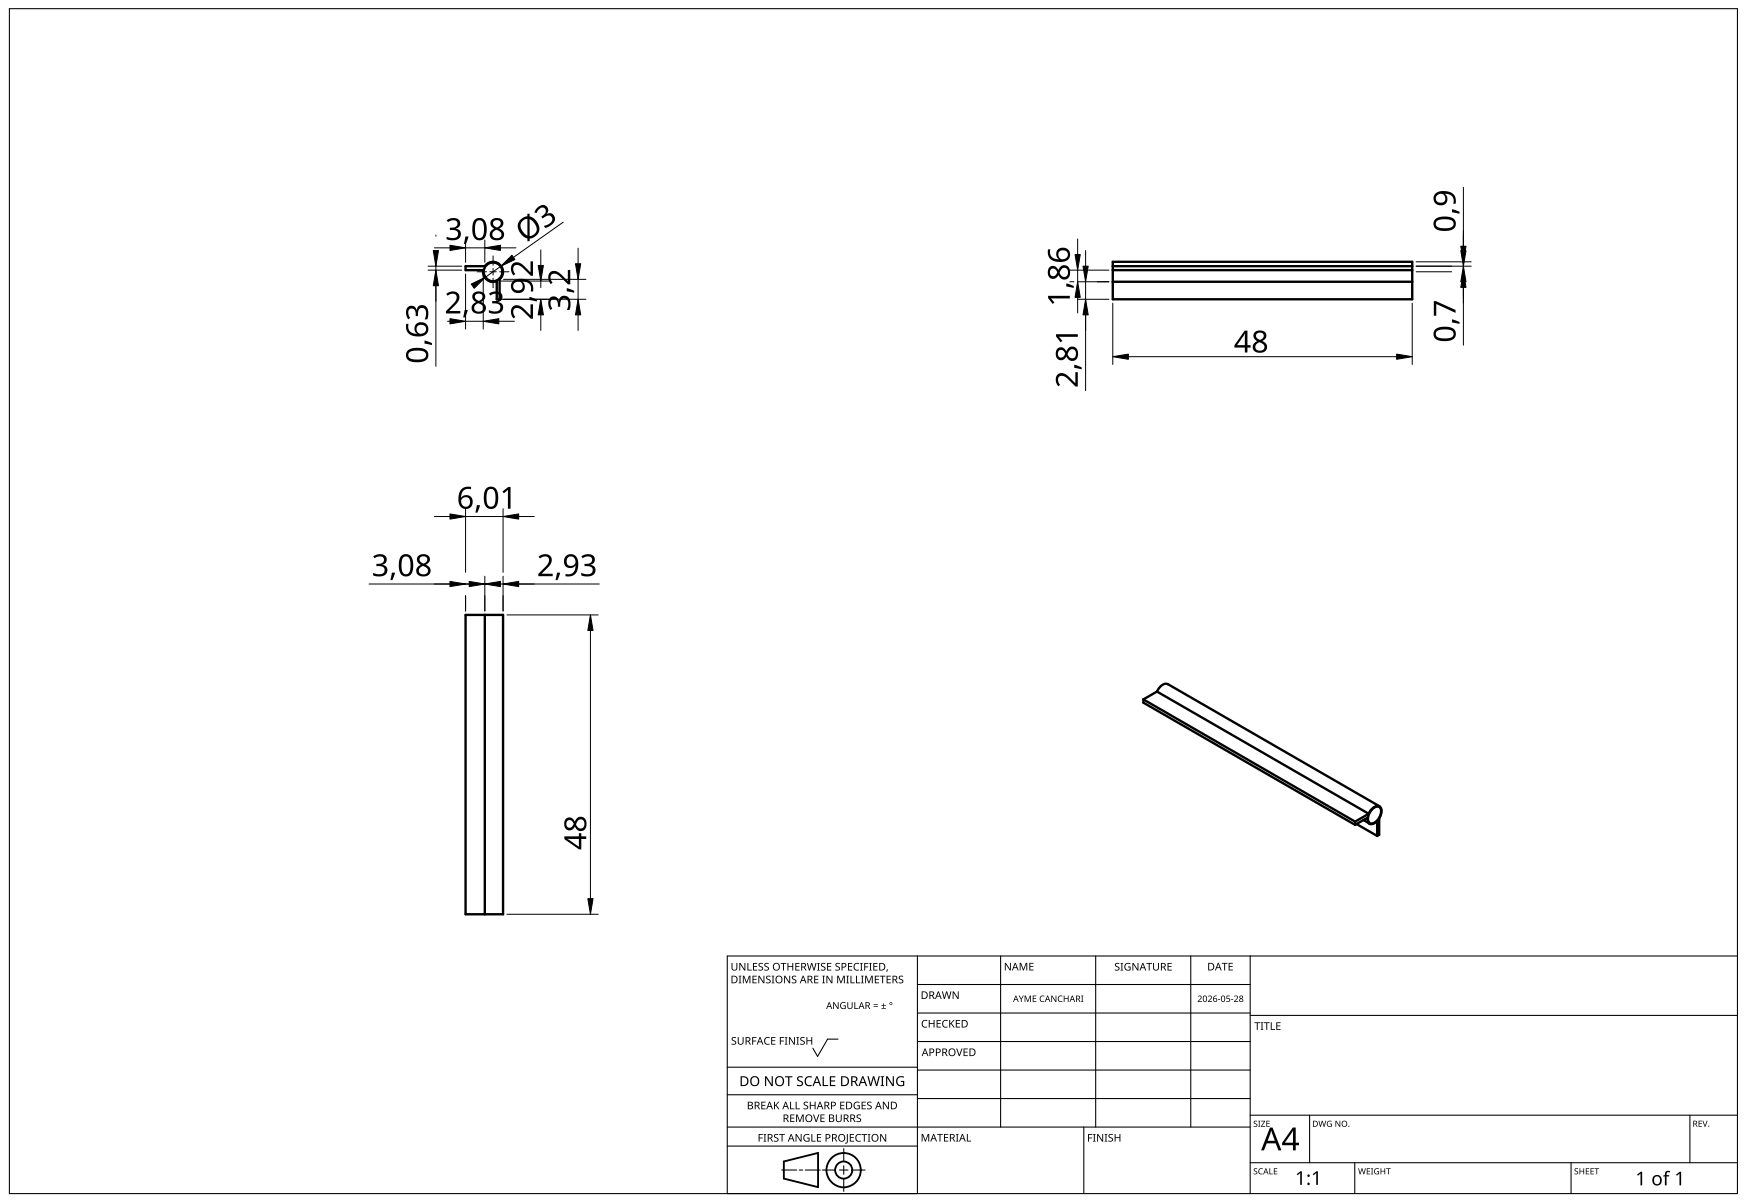
[picture p155: page 1]
