valenlysm29/FdD_EQUIPO02/Proyecto/Módulo Mecánico/version 2.0/Onshape/Planos/Caja Grande/Part 7 Caja Agua Drawing 1.pdf

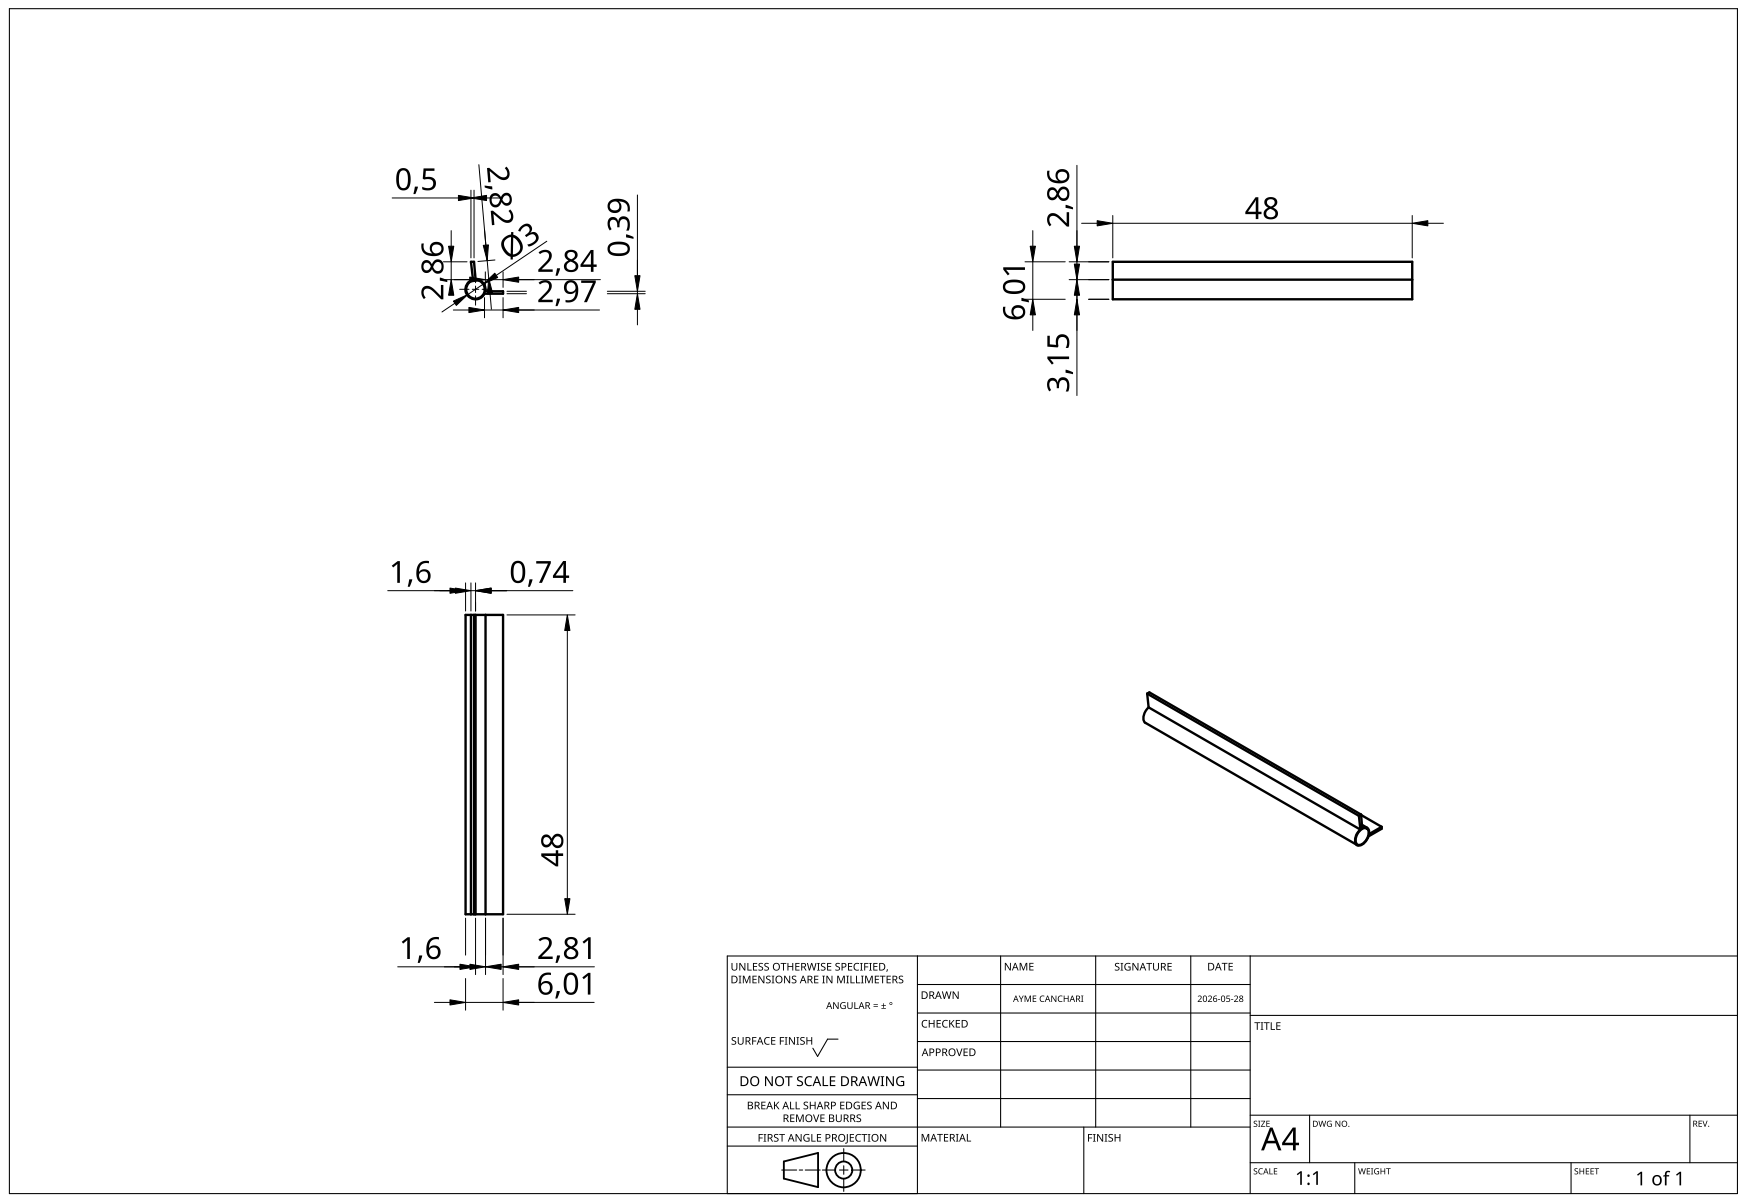
[picture p157: page 1]
