valenlysm29/FdD_EQUIPO02/Proyecto/Módulo Mecánico/version 2.0/Onshape/Planos/Caja pequeña (aire)/Part 1 Caja Aire Drawing.pdf

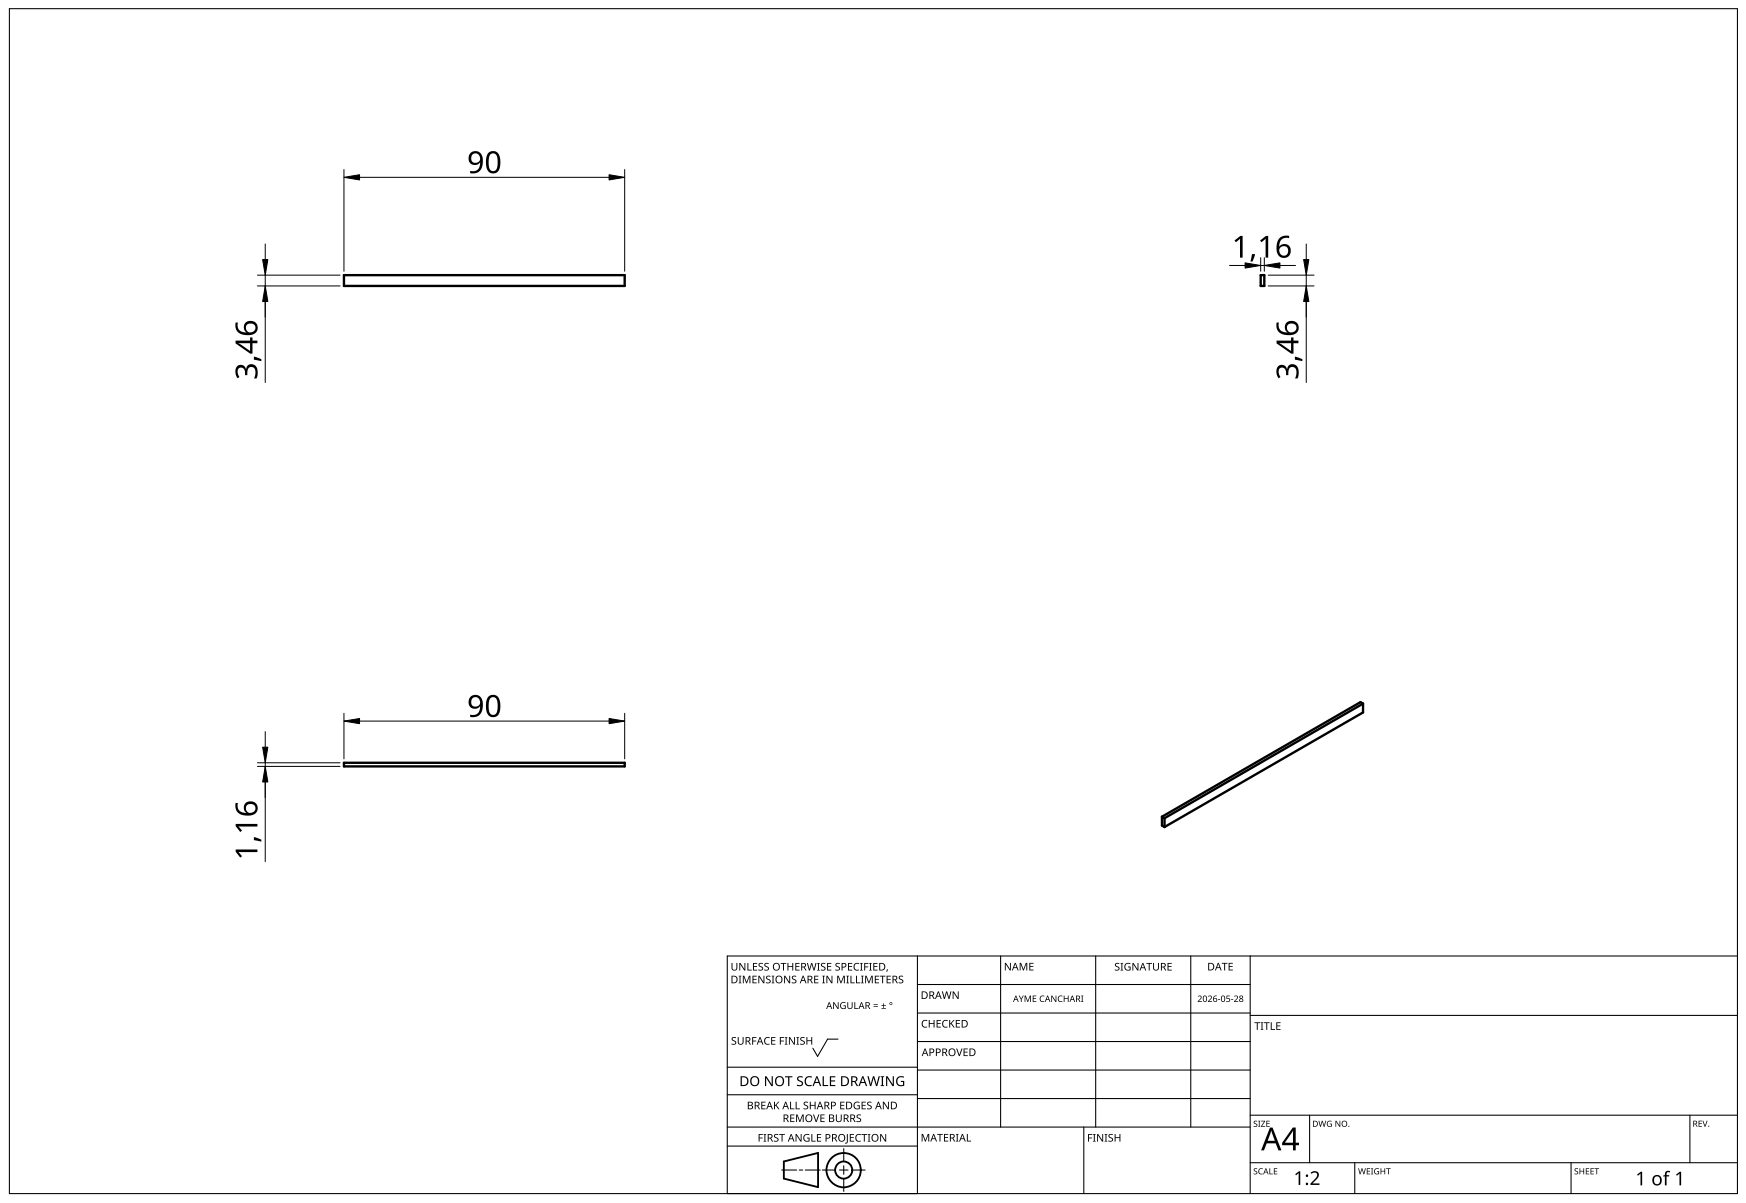
[picture p158: page 1]
