valenlysm29/FdD_EQUIPO02/Proyecto/Módulo Mecánico/version 2.0/Onshape/Planos/Caja pequeña (aire)/Part 2 Caja Aire Drawing 2.pdf

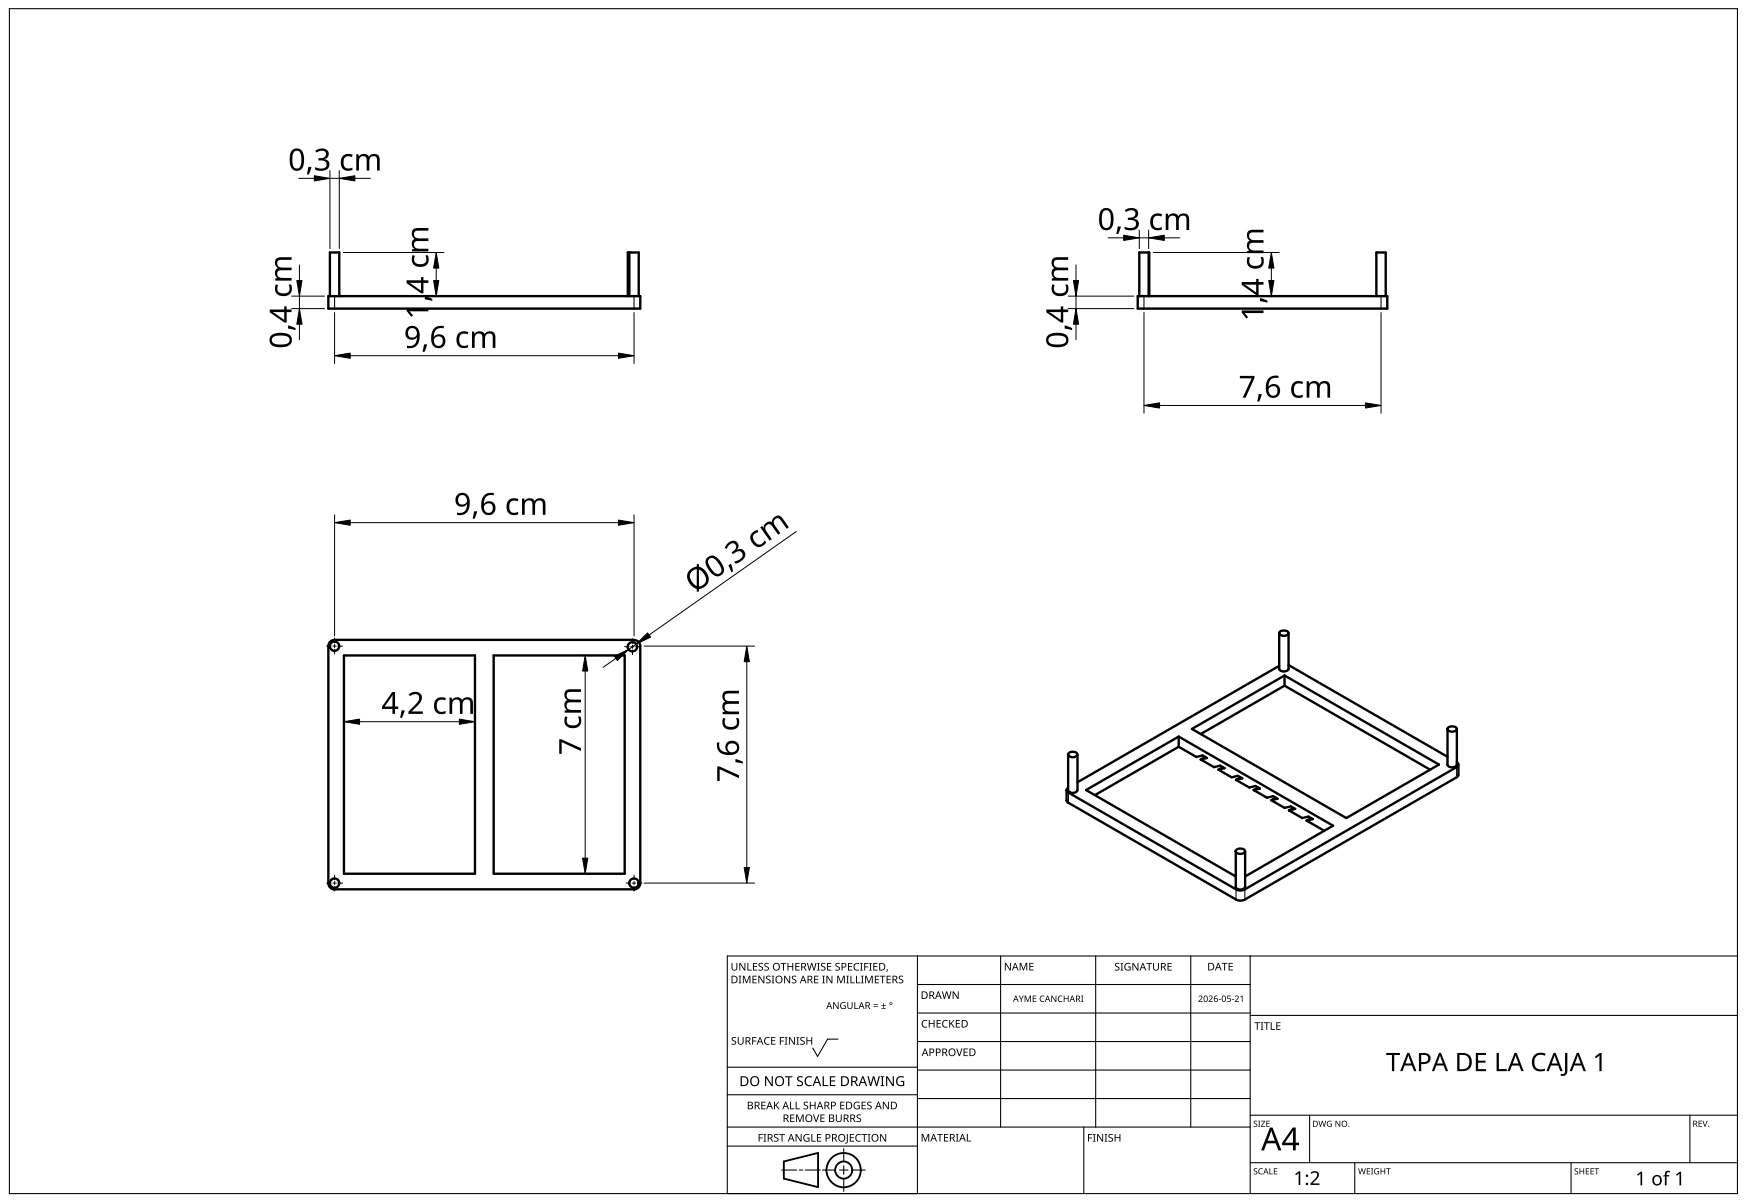
[picture p159: page 1]
