valenlysm29/FdD_EQUIPO02/Proyecto/Módulo Mecánico/version 2.0/Onshape/Planos/Caja pequeña (aire)/Part 3 Caja Aire Drawing 3.pdf

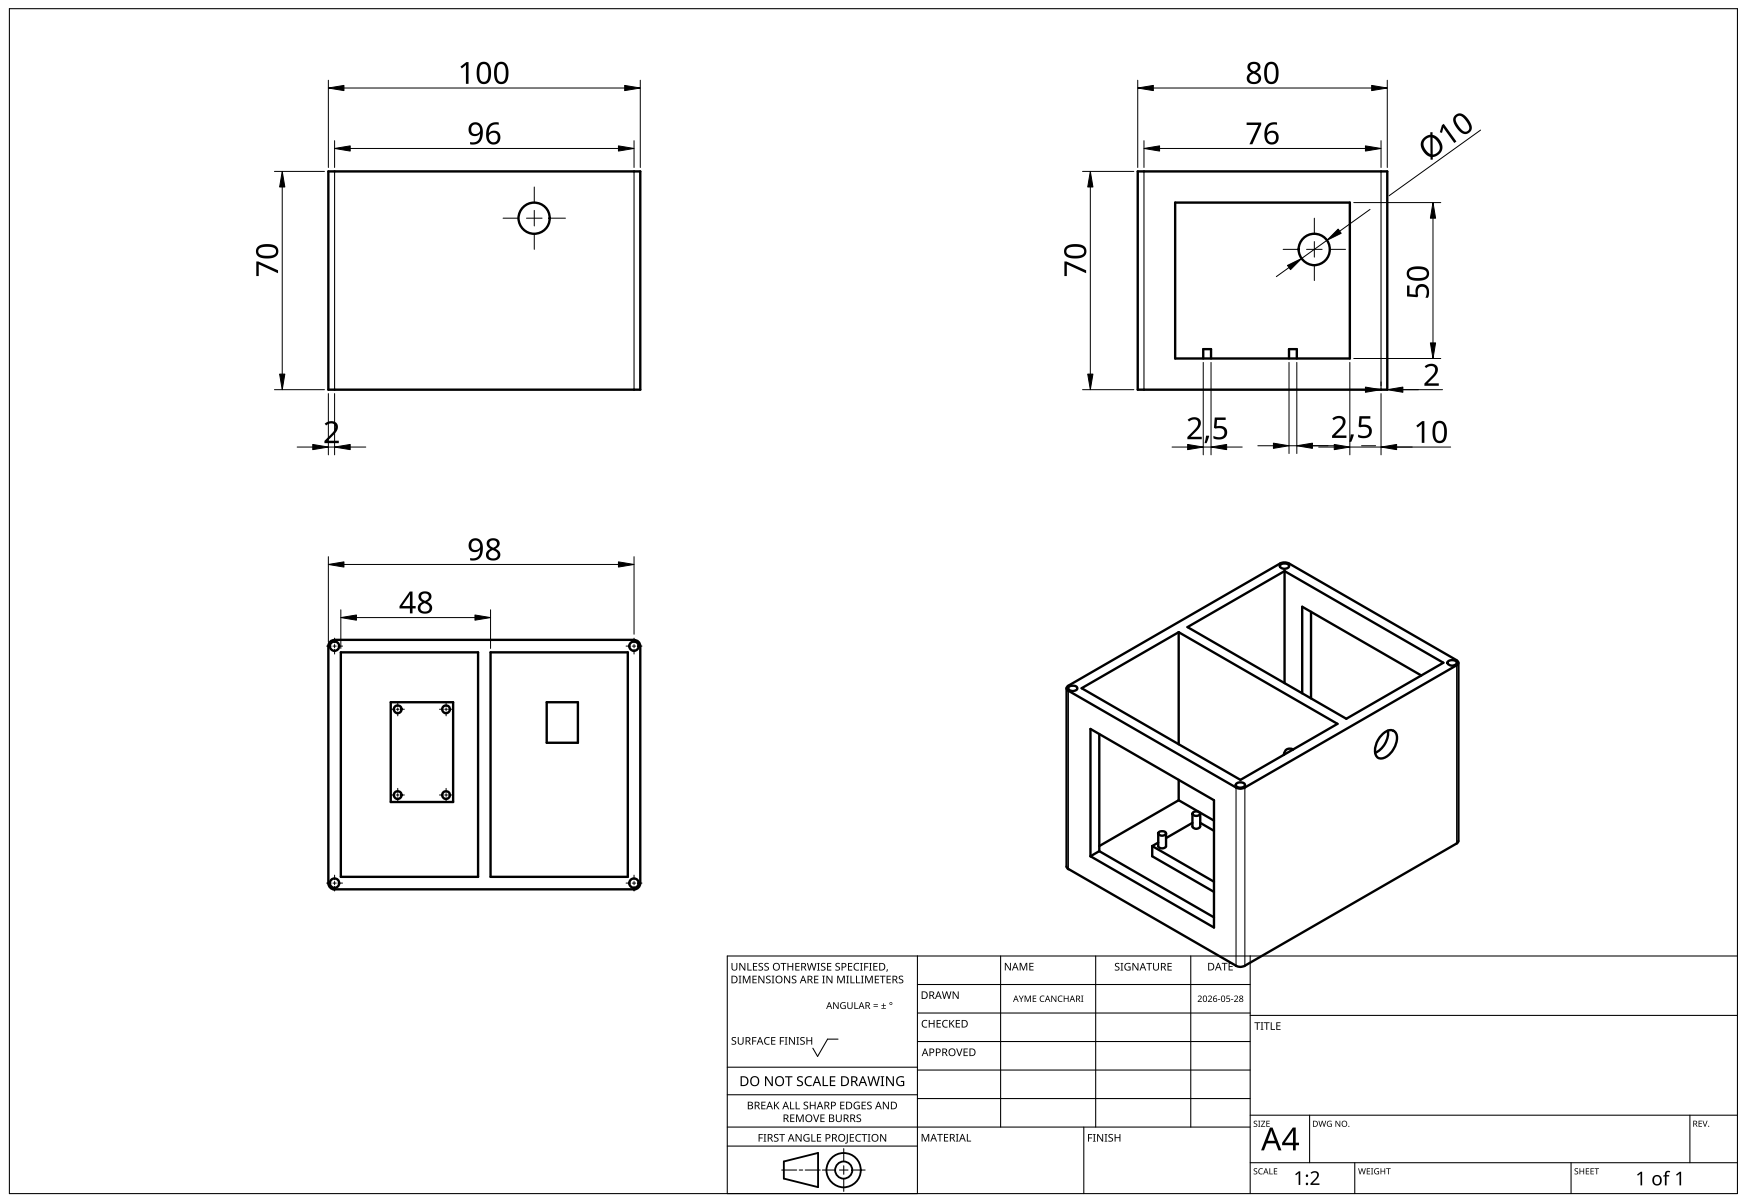
[picture p160: page 1]
